benoitGIRAUD/NGL_PROTO_ST/Output/PNG/NGL_Proto_BOT.png

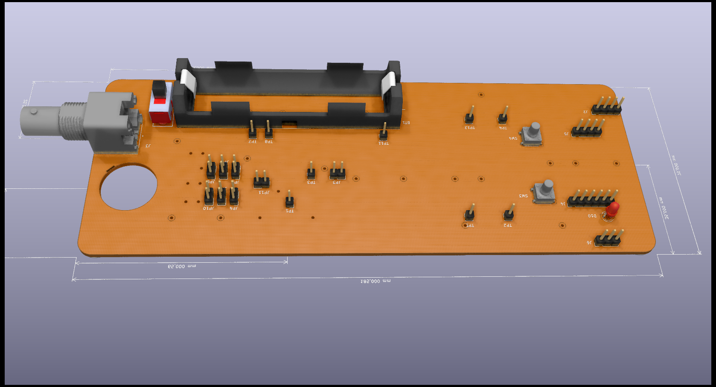
Output/PNG/NGL_Proto_BOT.png
