benoitGIRAUD/NGL_PROTO_ST/Output/PNG/NGL_Proto_TOP.png

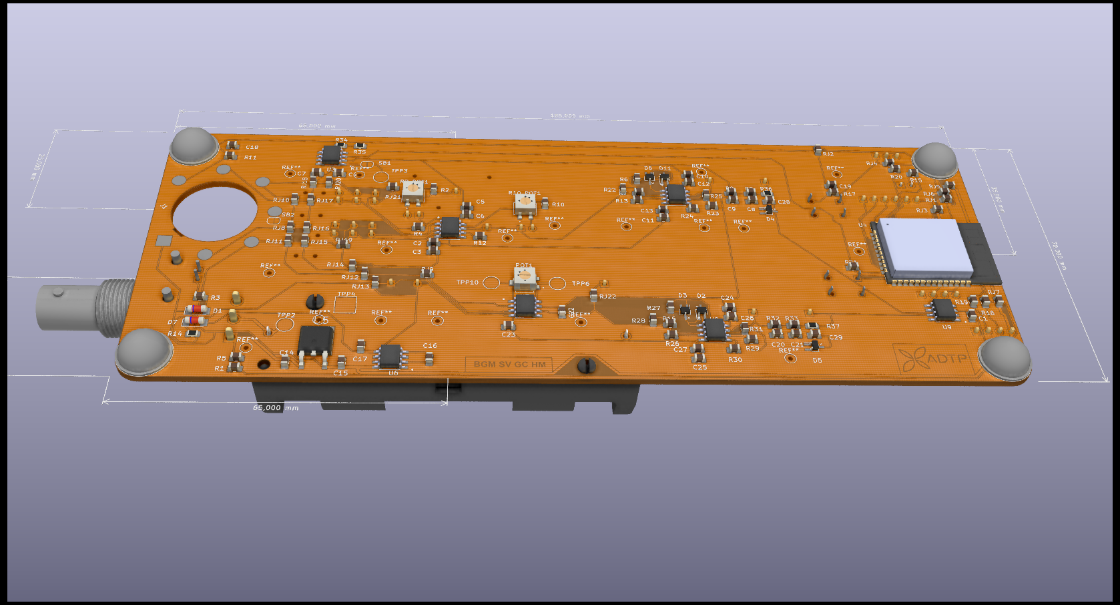
Output/PNG/NGL_Proto_TOP.png
