benoitGIRAUD/NGL_PROTO_ST/Lib_NGL_Proto/3224X-1-103E.STEP

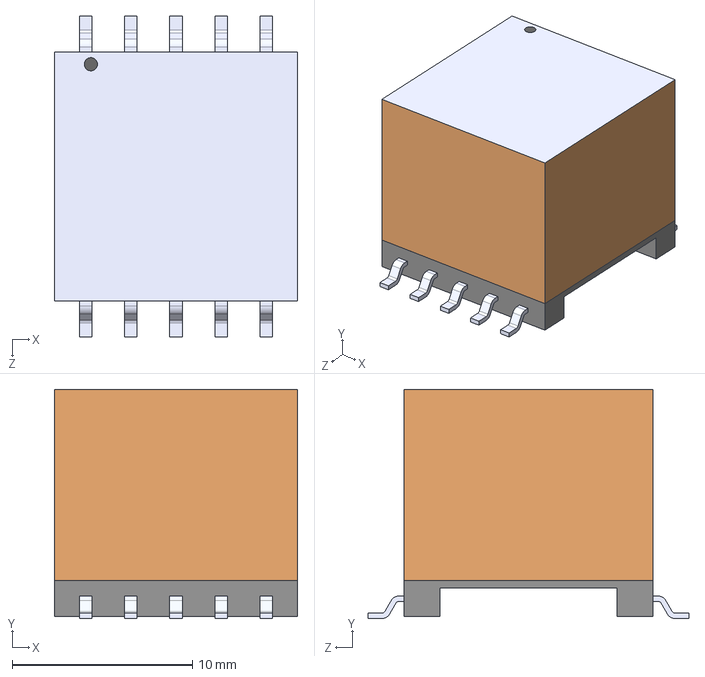
[picture p25: CAD file, 2022-05-25]
Lib_NGL_Proto/3224X-1-103E.STEP
13.5 x 12.7 x 17.8 mm
