benoitGIRAUD/NGL_PROTO_ST/Lib_NGL_Proto/5227161-2.step

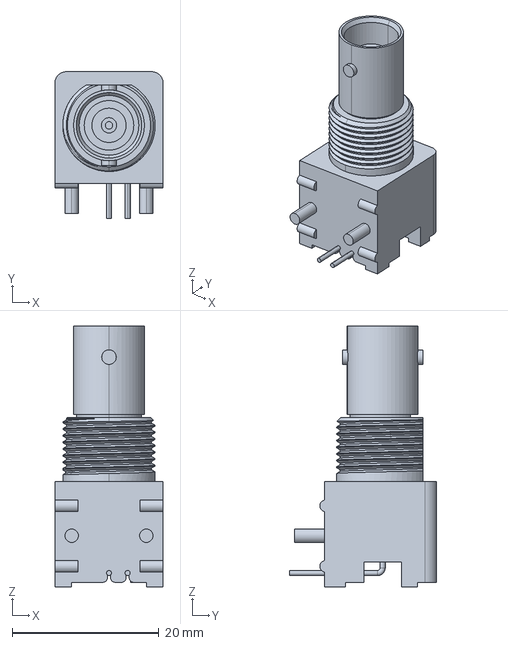
[picture p26: CAD file, 2022-05-25]
Lib_NGL_Proto/5227161-2.step
14.8 x 20.0 x 35.6 mm
