benoitGIRAUD/NGL_PROTO_ST/Output/SCH/NGL_Proto_PROD.pdf

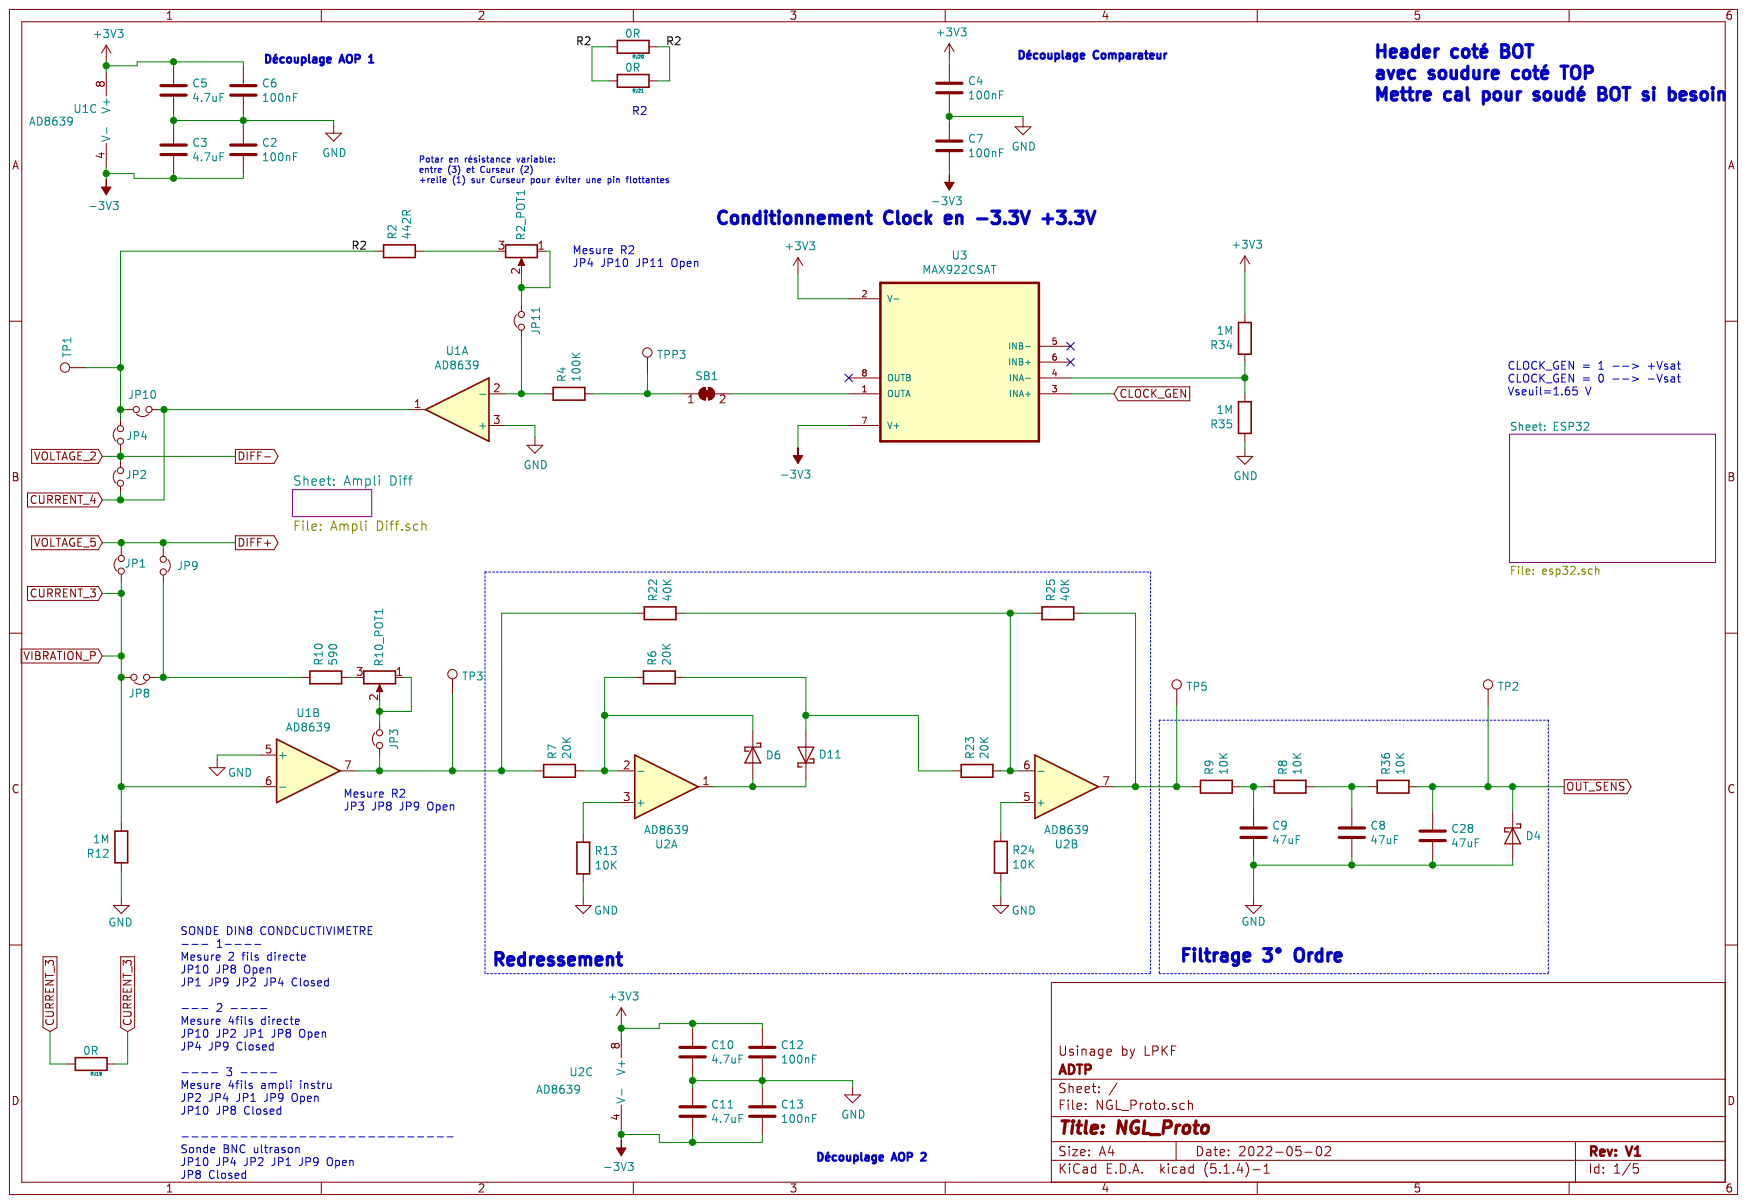
[picture p29: page 1]

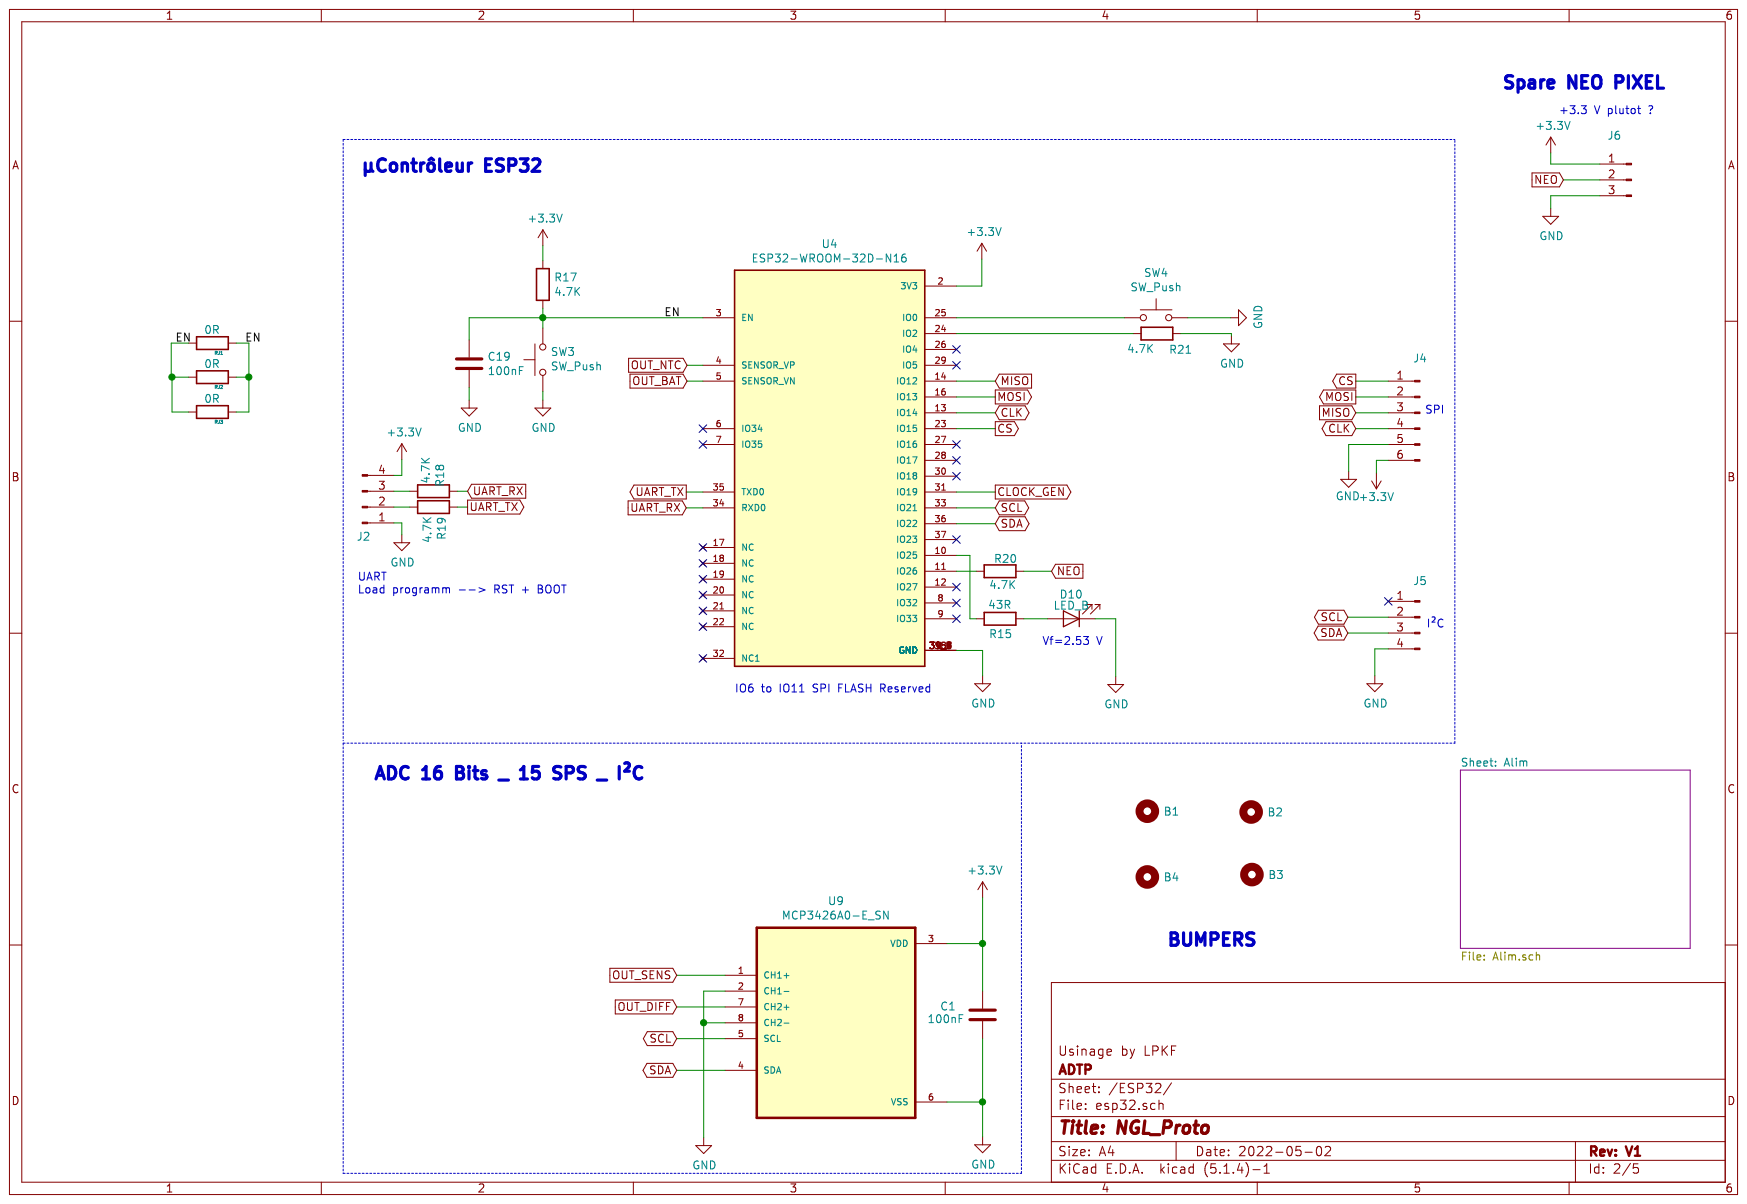
[picture p30: page 2]

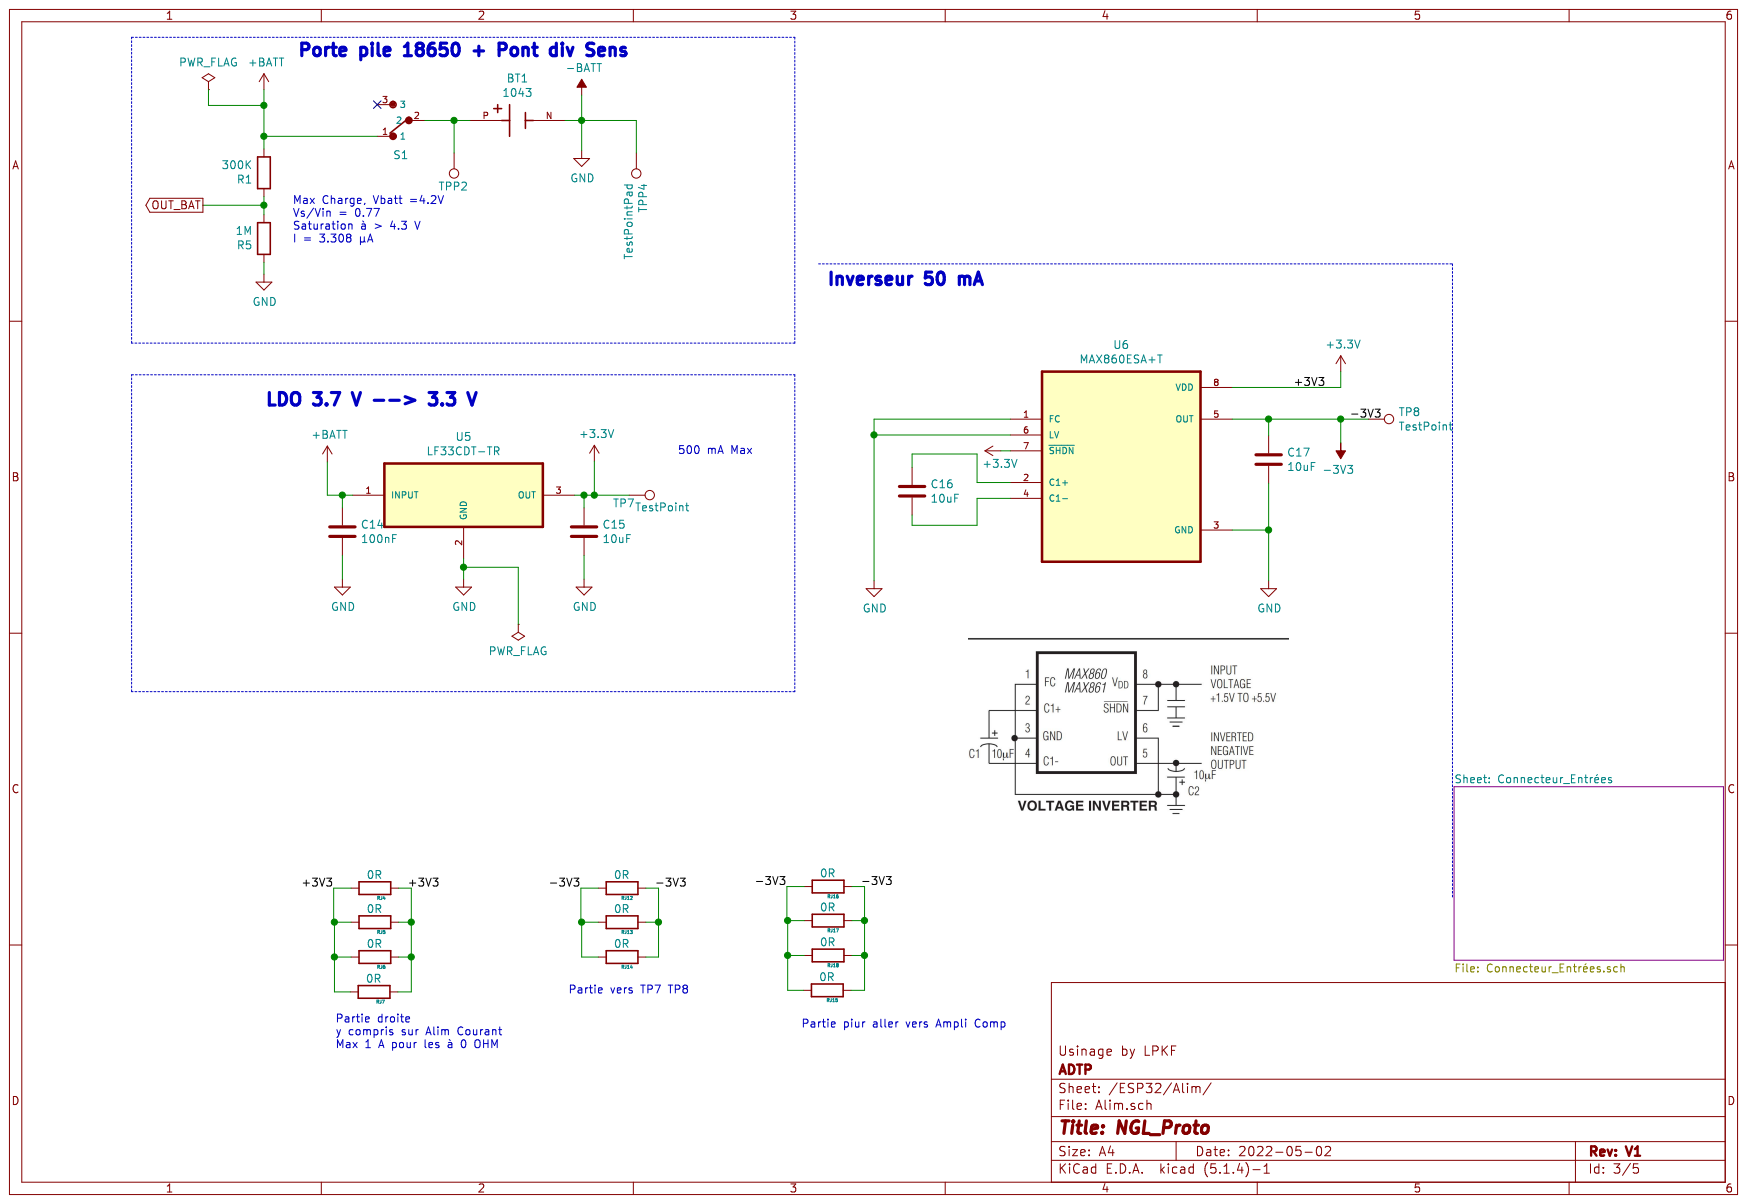
[picture p31: page 3]

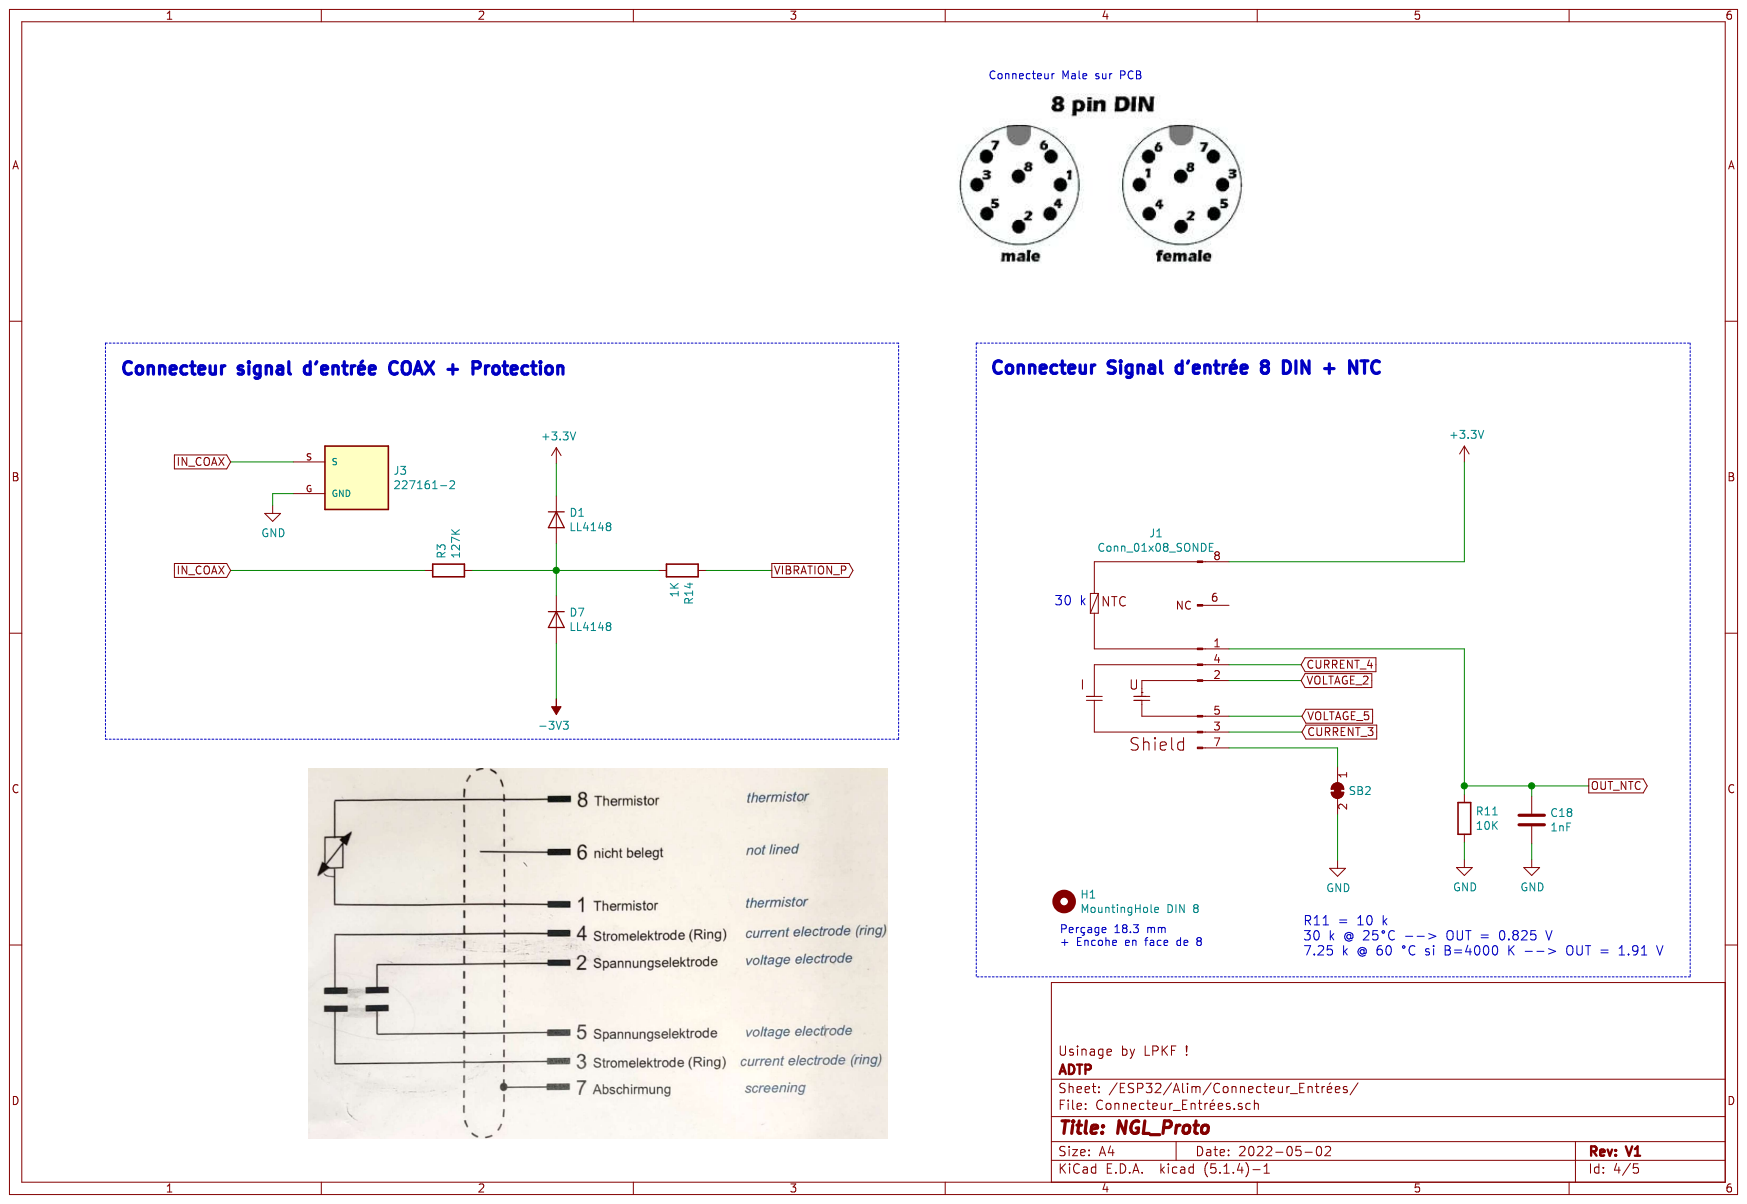
[picture p32: page 4]

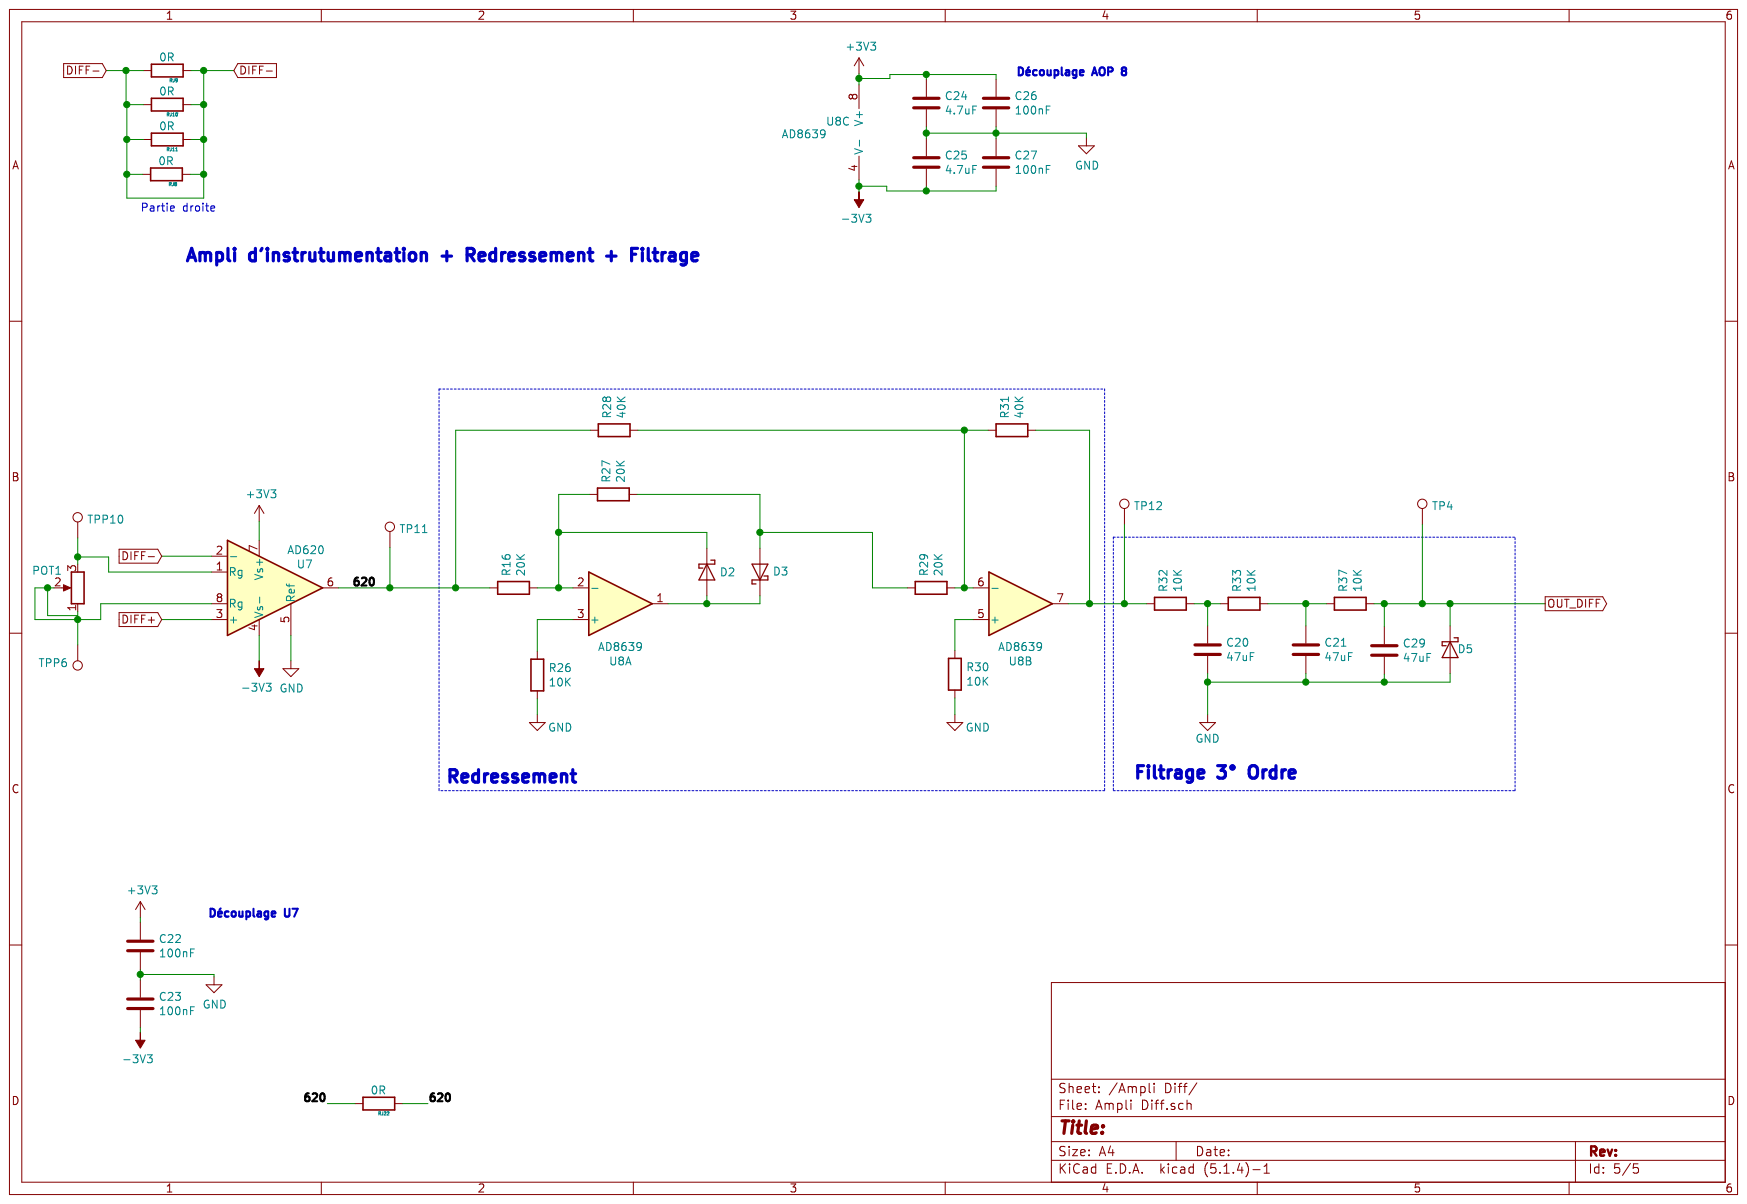
[picture p33: page 5]
