benoitGIRAUD/NGL_PROTO_ST/Output/SCH/NGL_Proto_V1.pdf

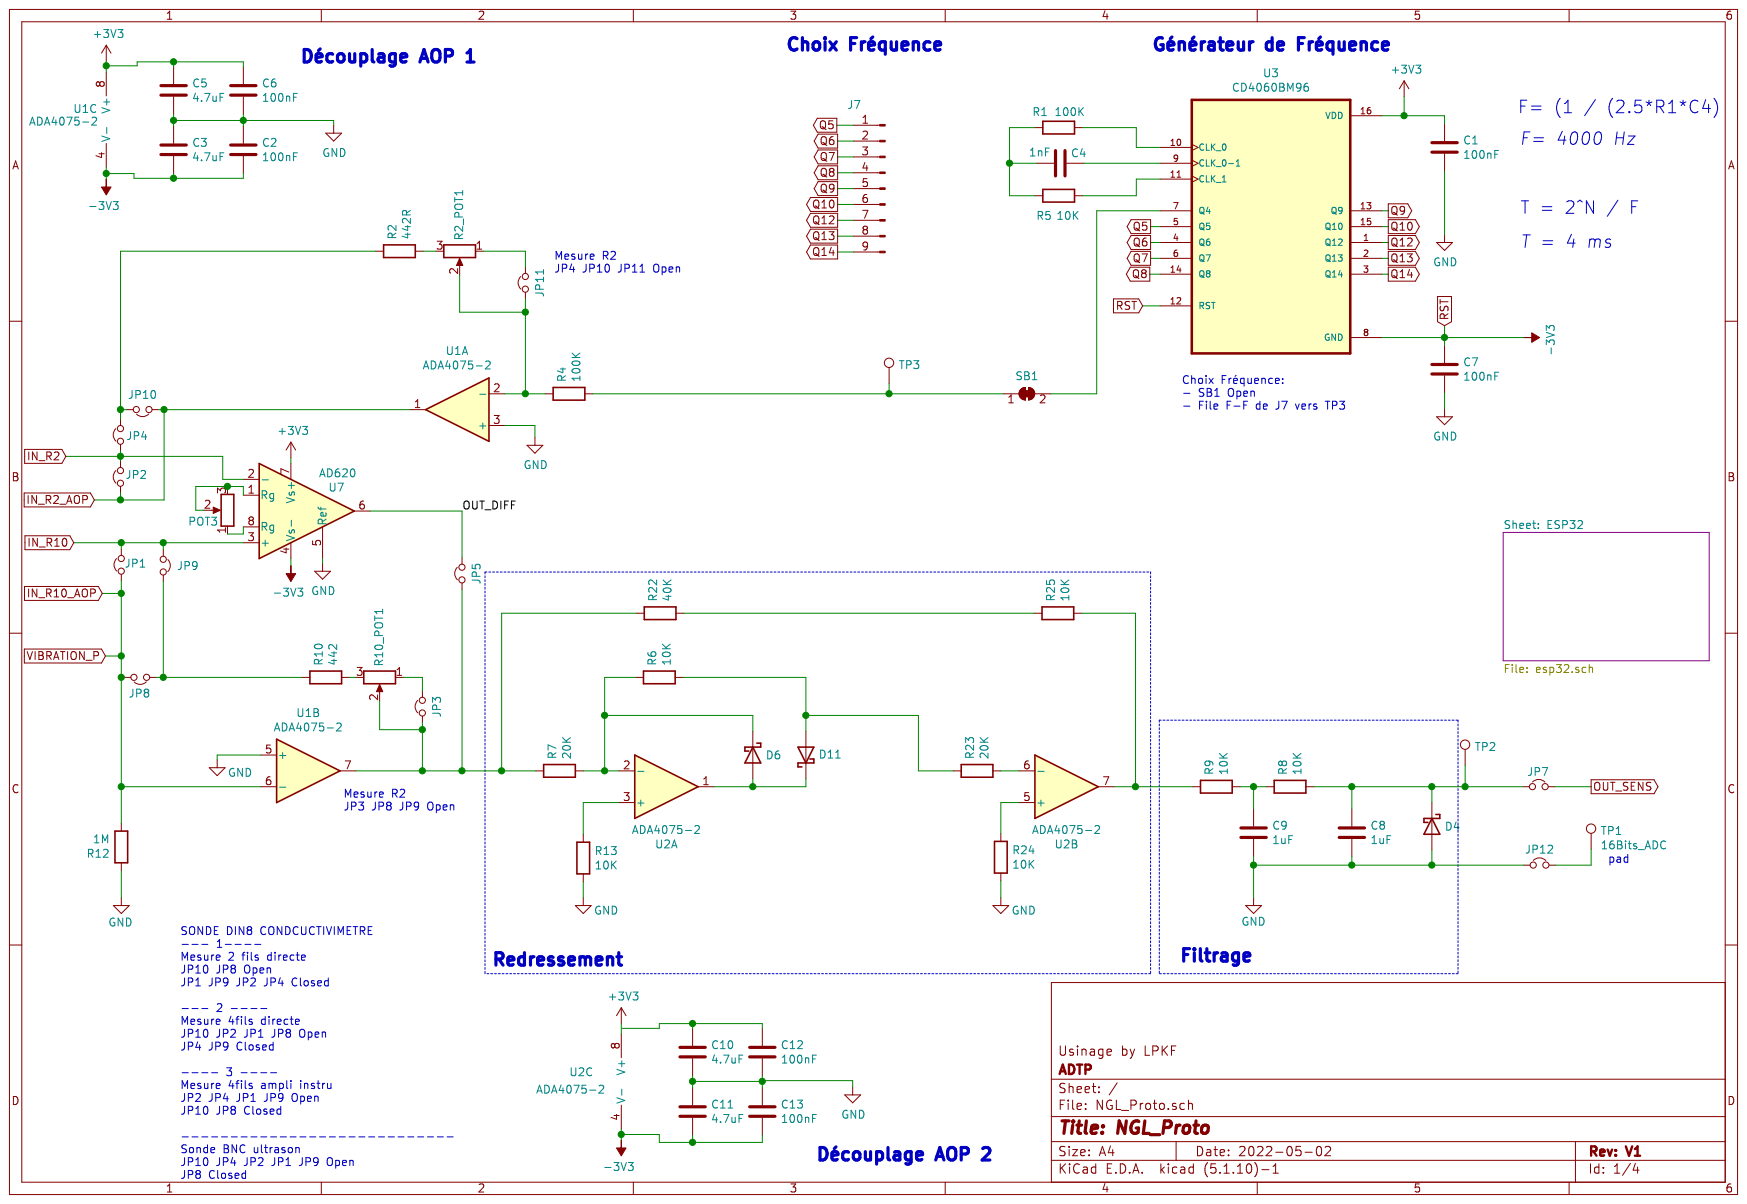
[picture p34: page 1]

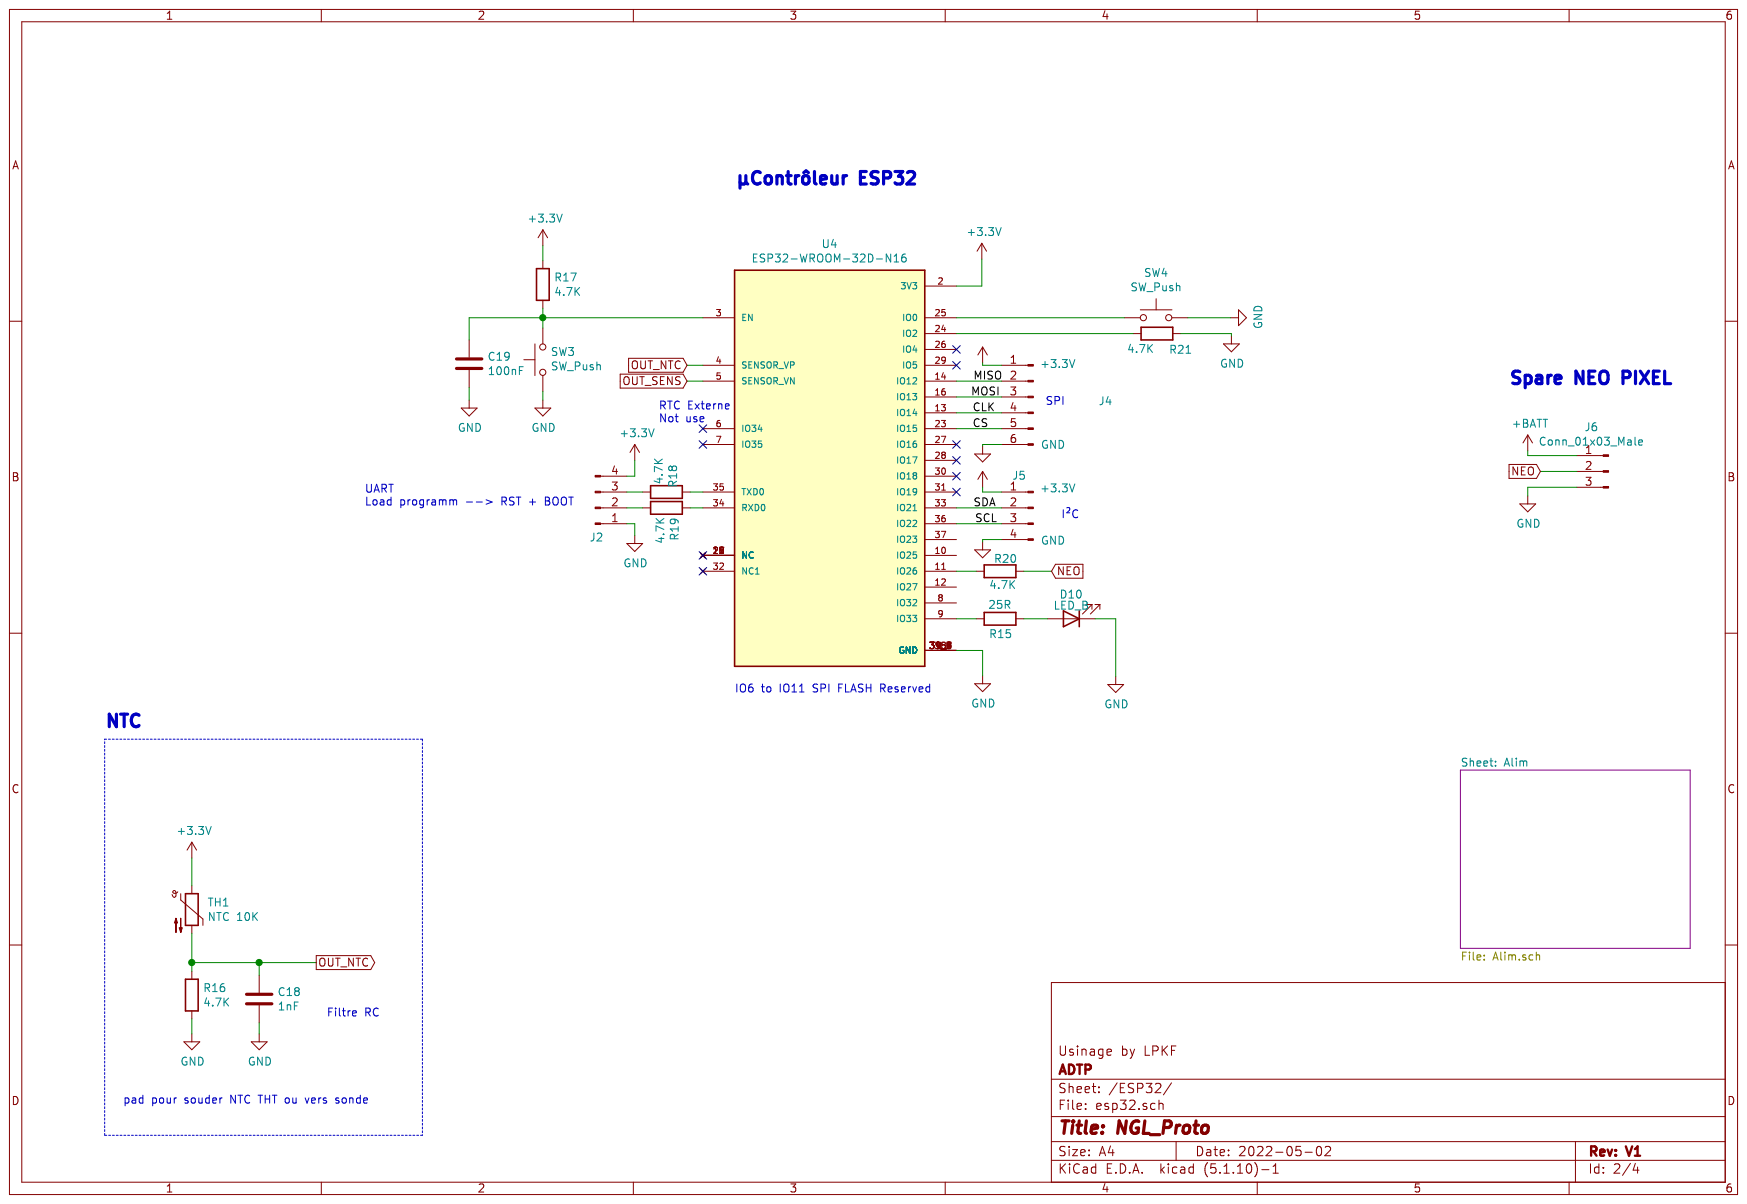
[picture p35: page 2]

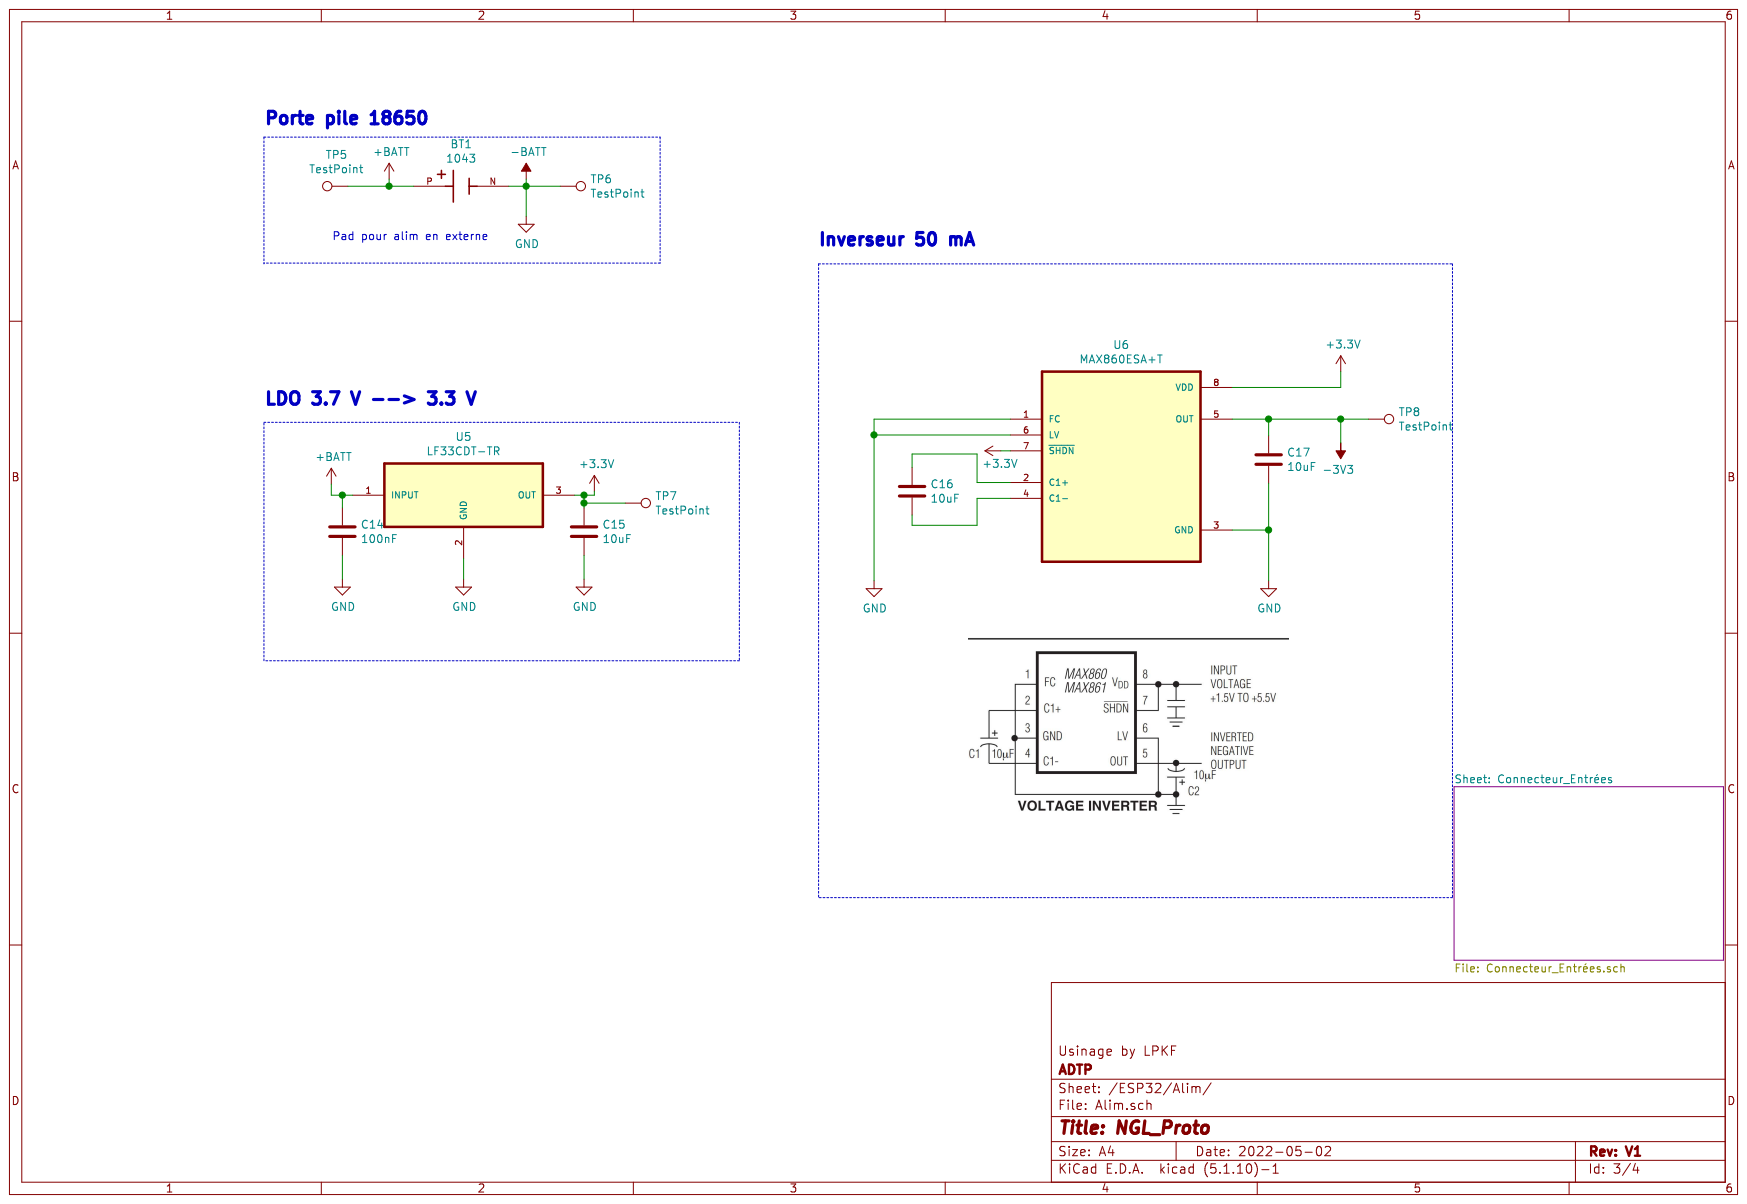
[picture p36: page 3]

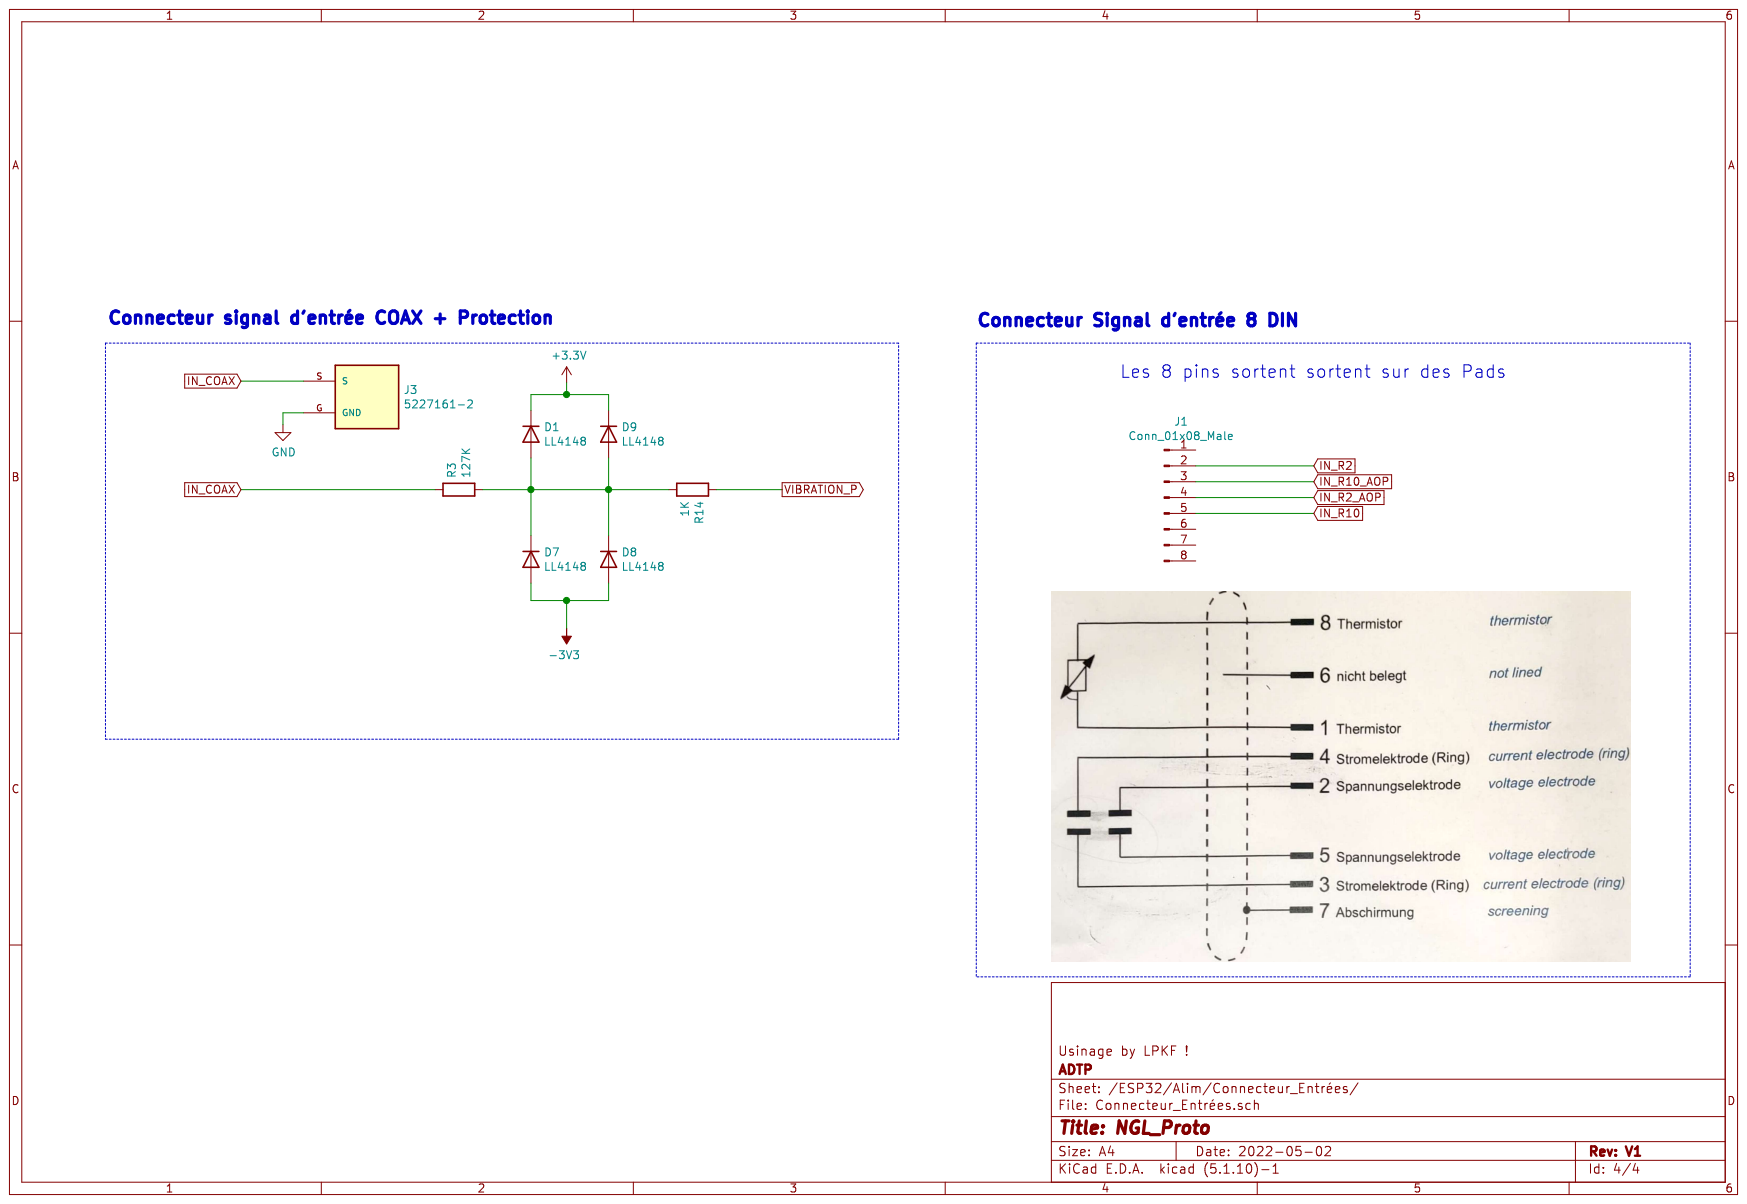
[picture p37: page 4]
