benoitGIRAUD/NGL_PROTO_ST/Output/SCH/NGL_Proto_V1_11-05.pdf

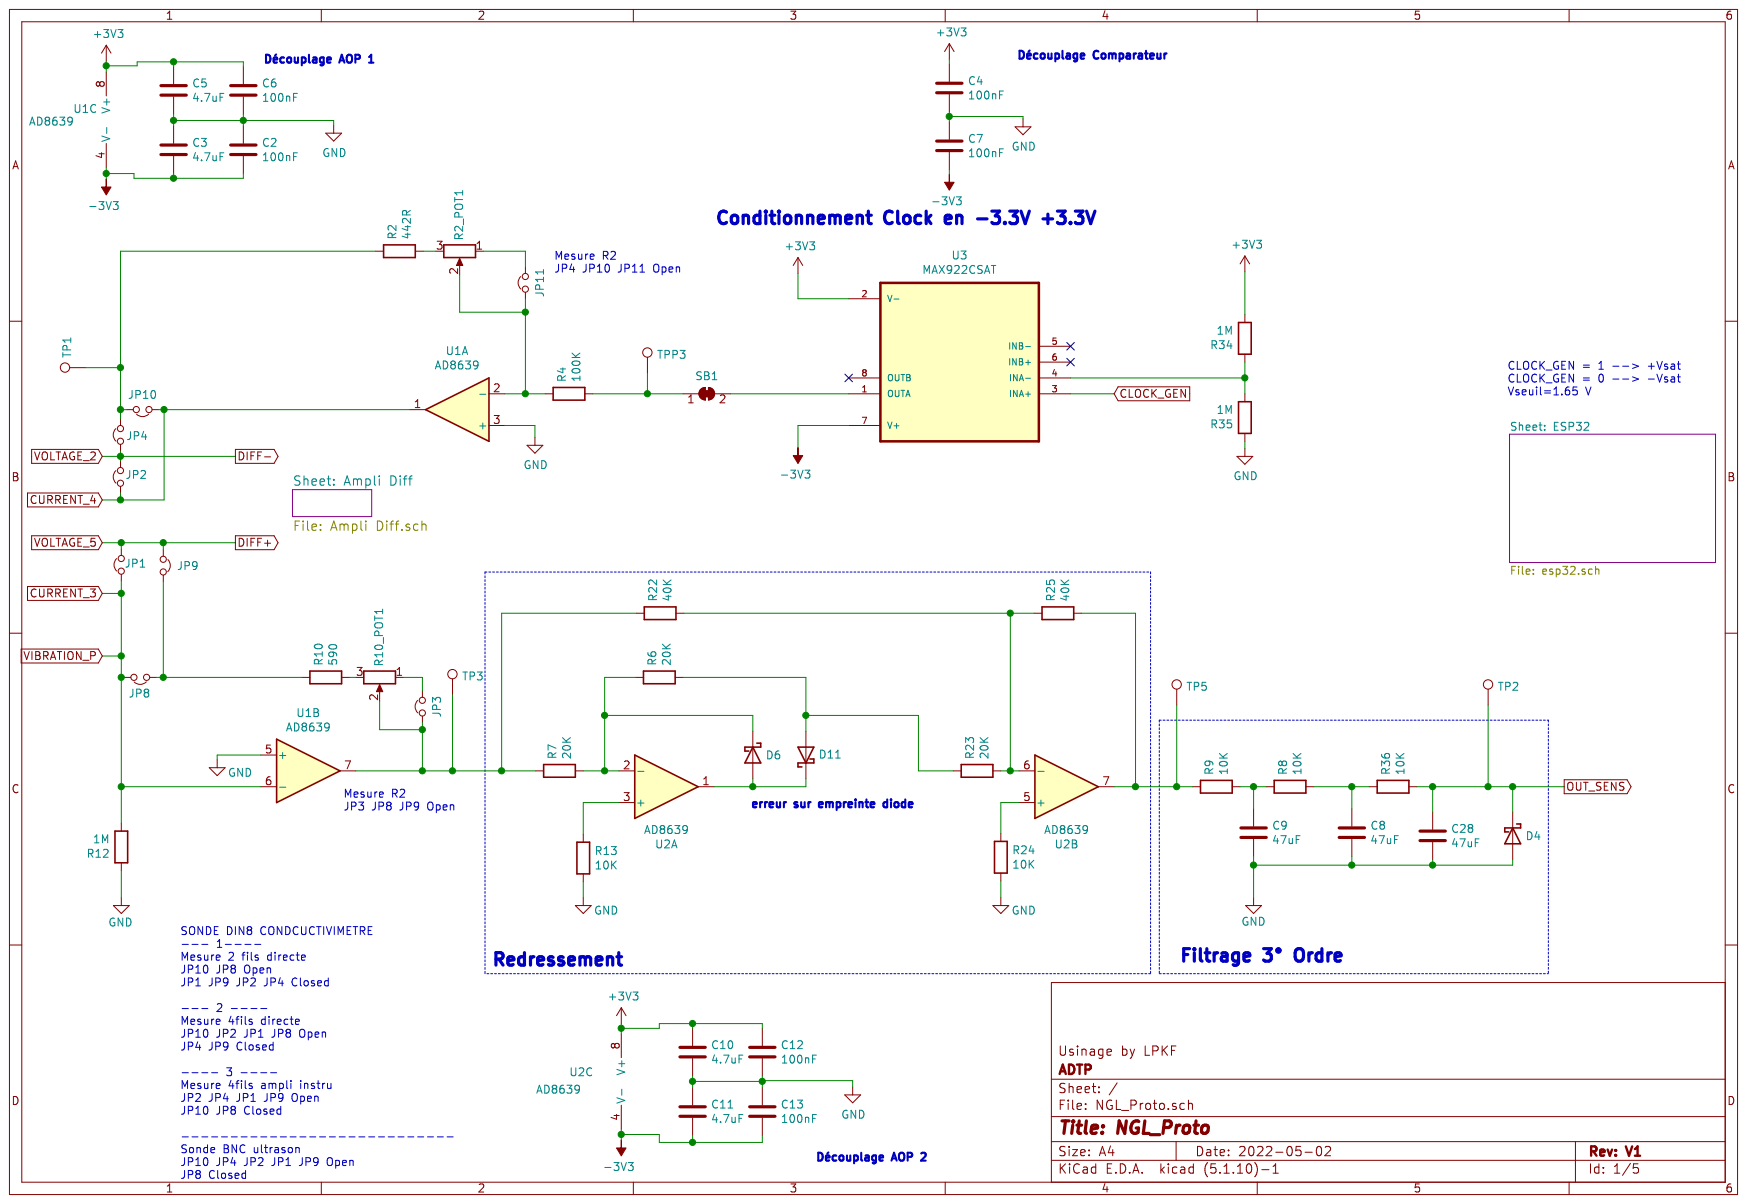
[picture p38: page 1]

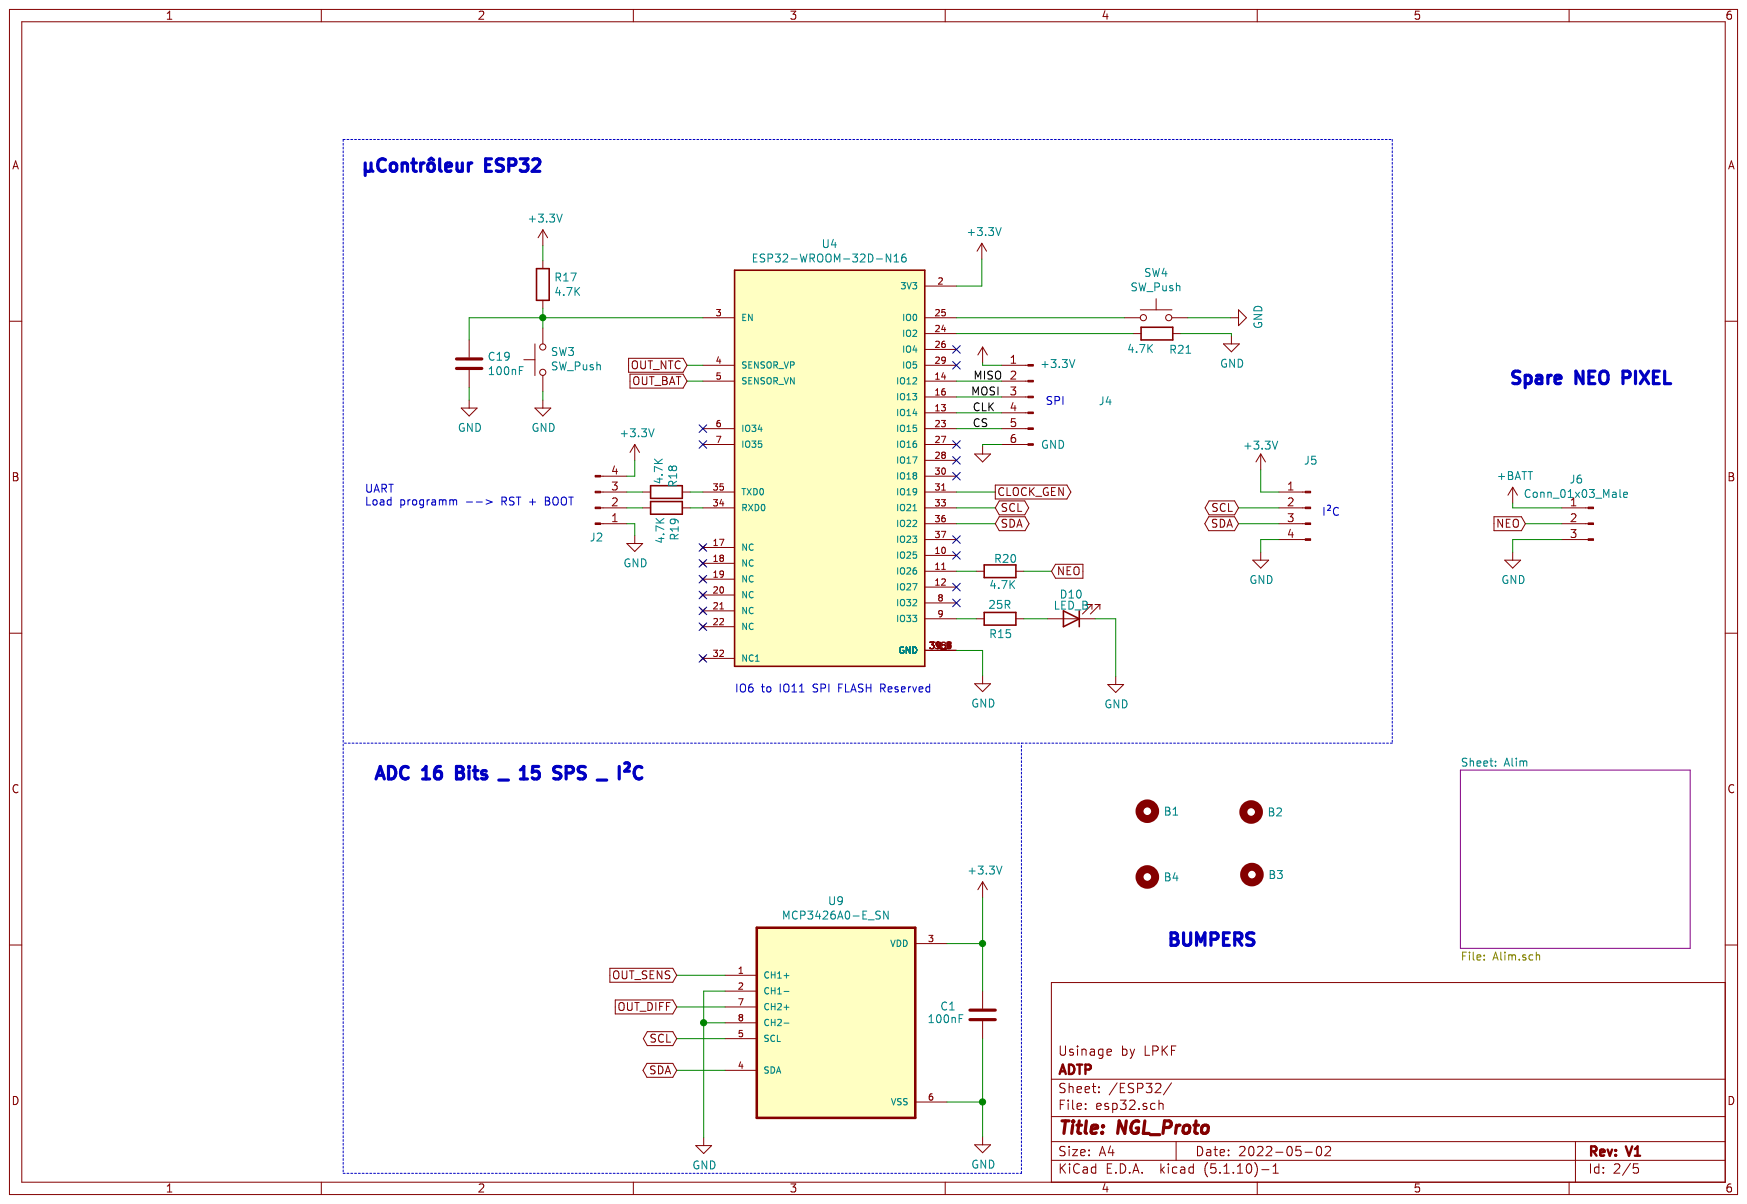
[picture p39: page 2]

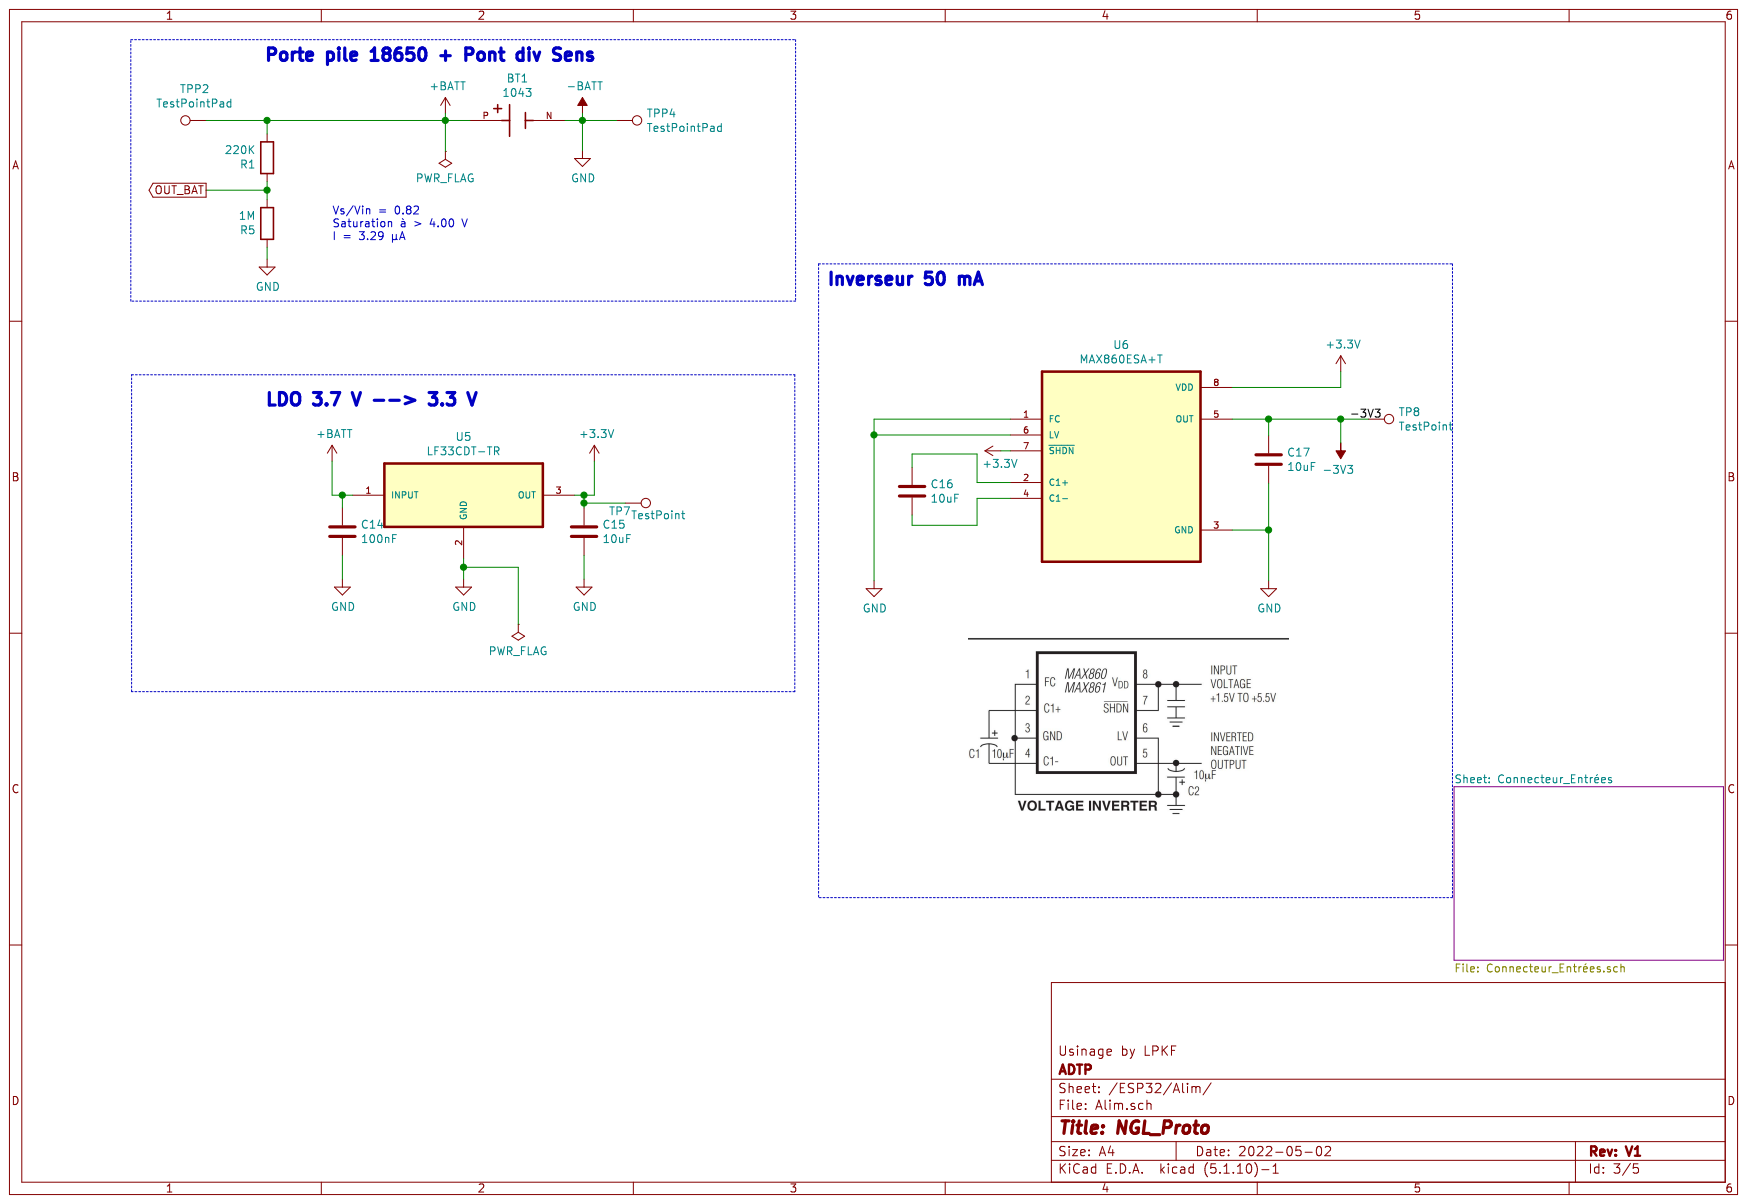
[picture p40: page 3]

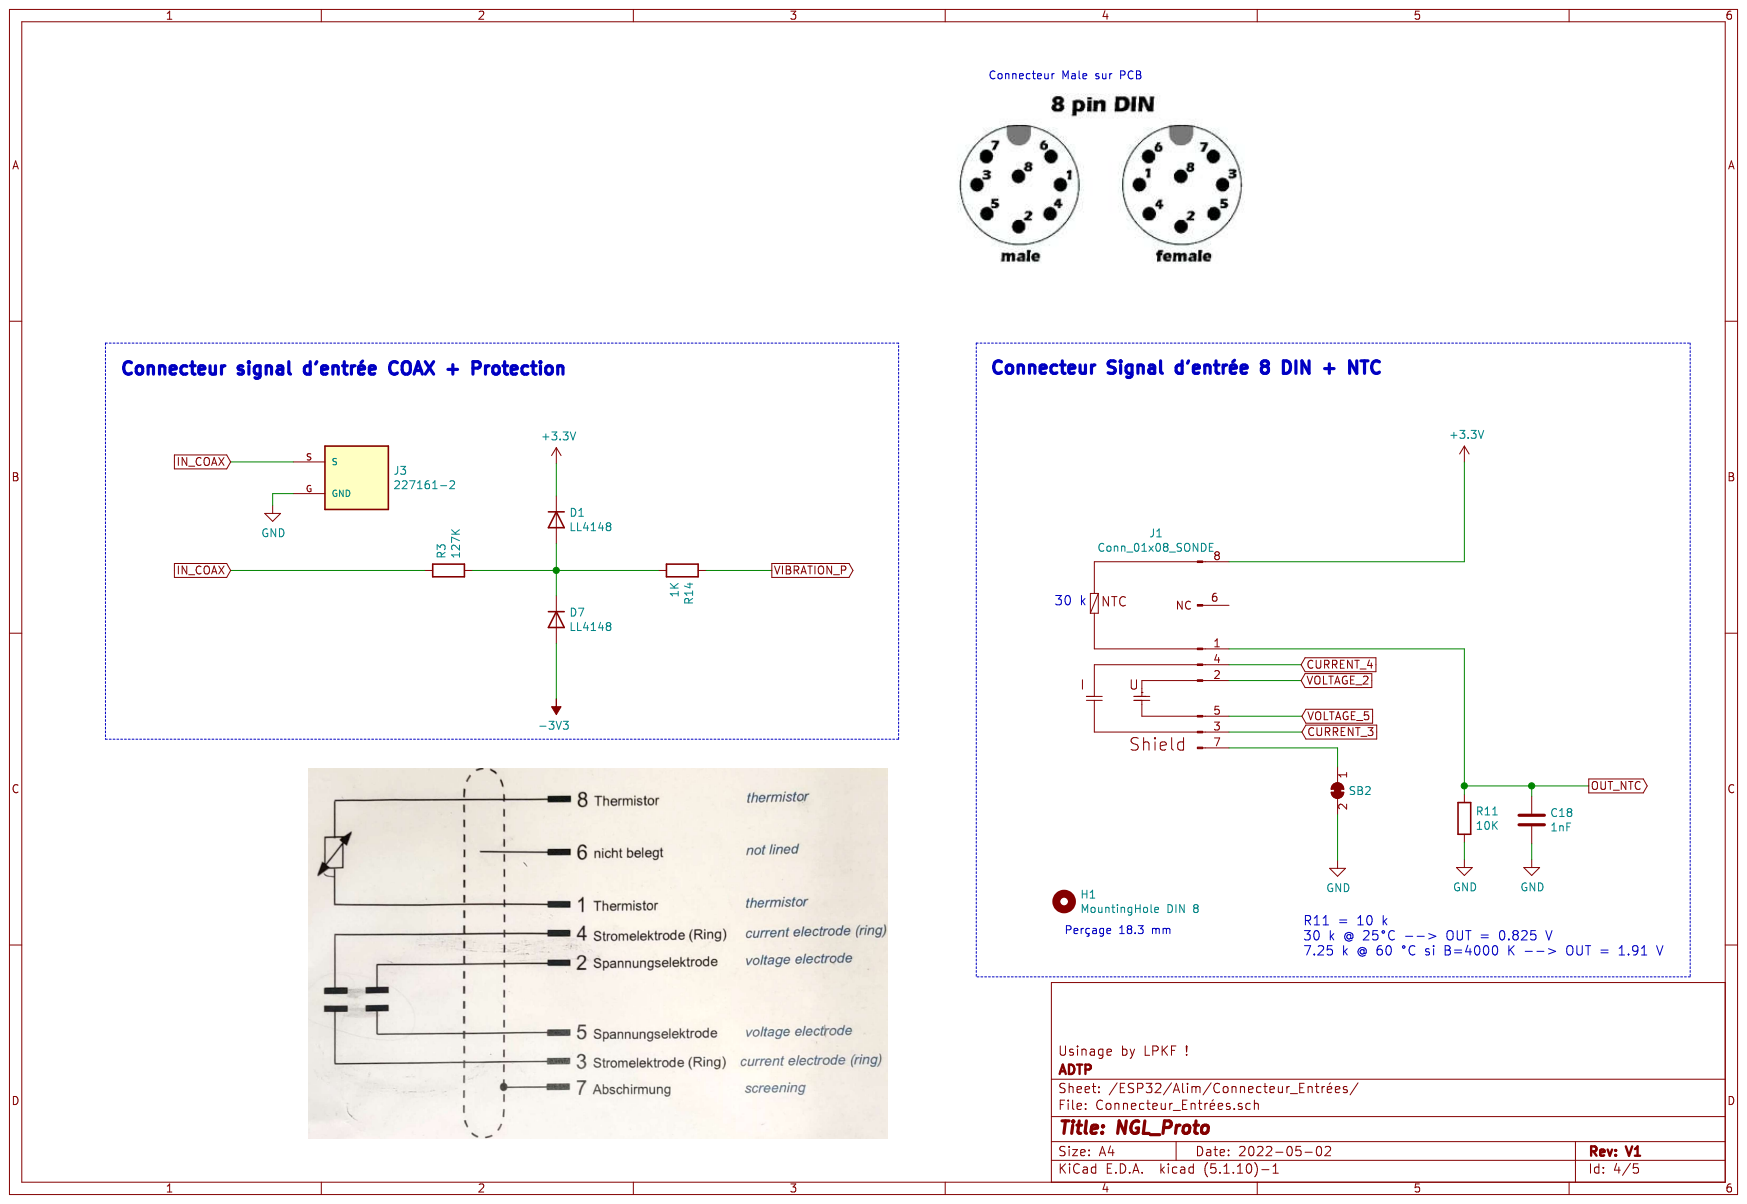
[picture p41: page 4]

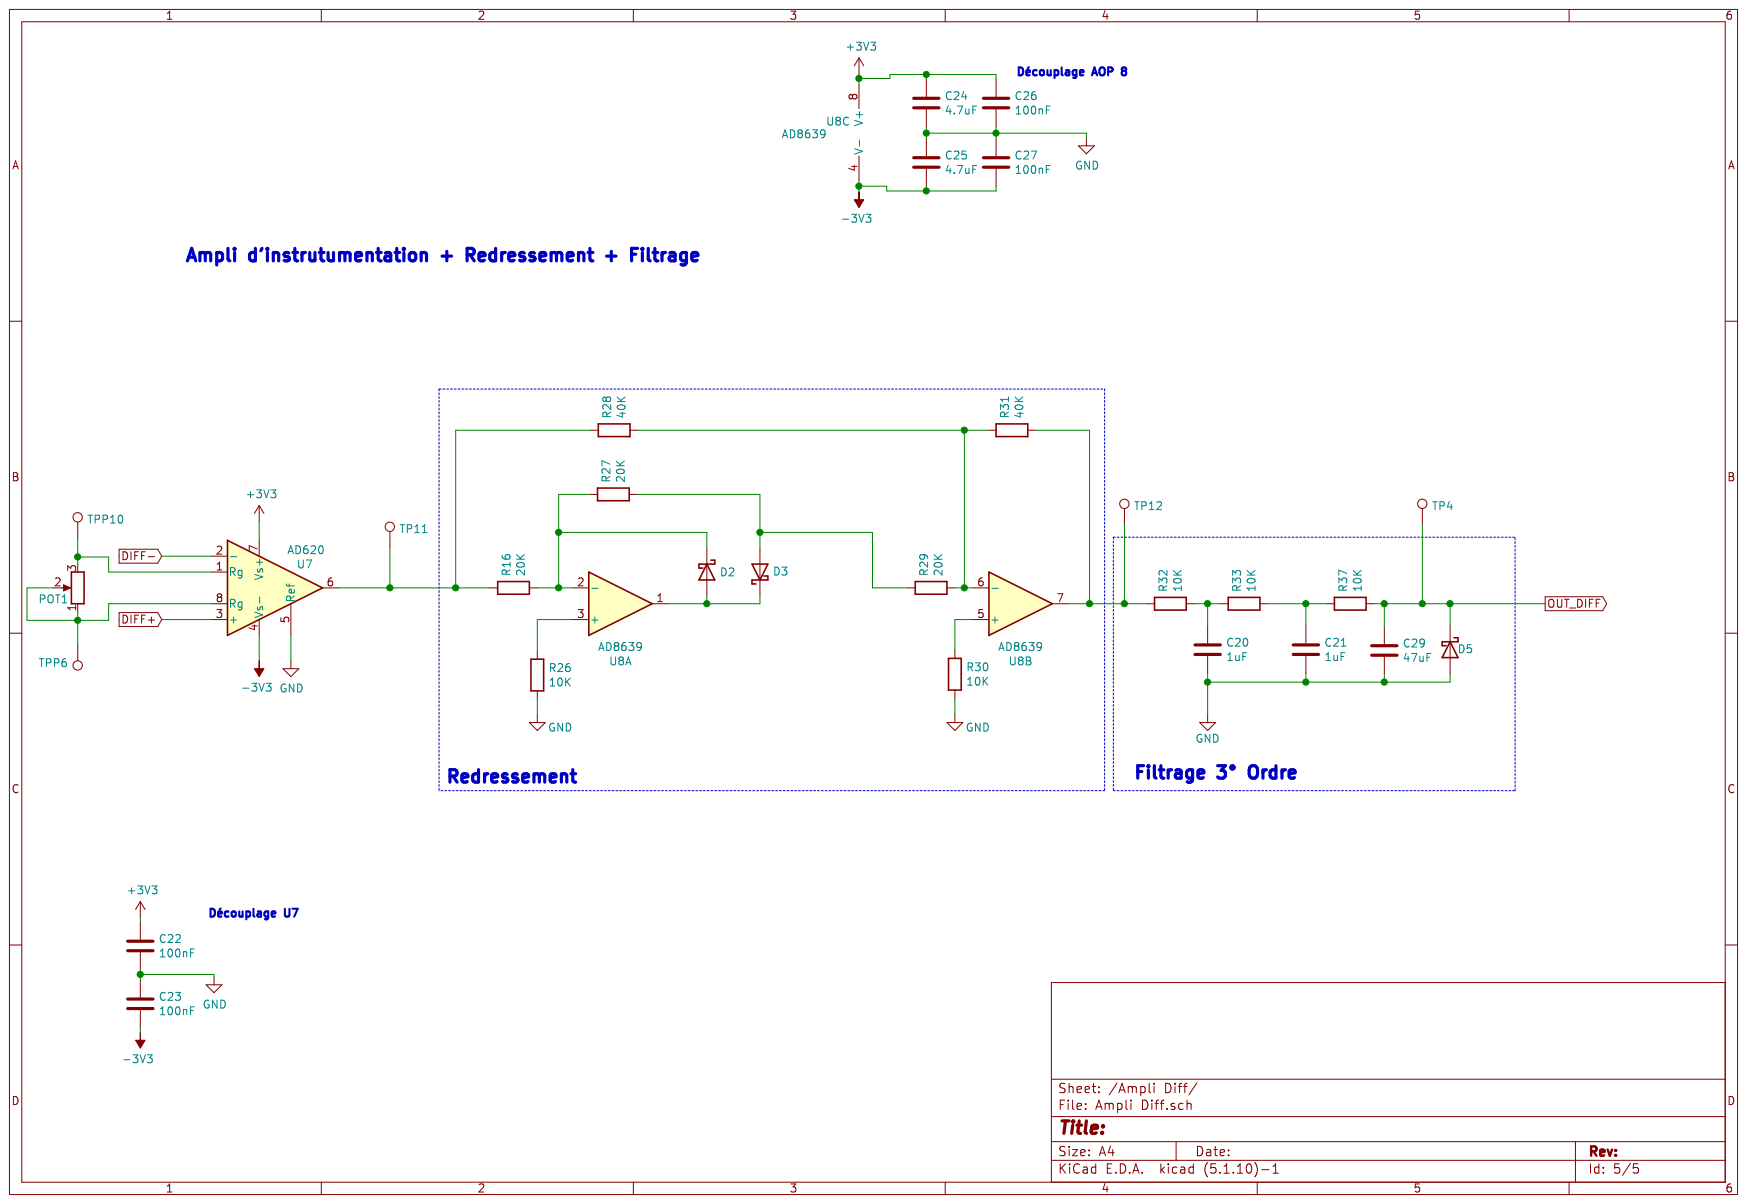
[picture p42: page 5]
