benoitGIRAUD/NGL_PROTO_ST/Output/SCH/NGL_Proto_V1_11-05_v2.pdf

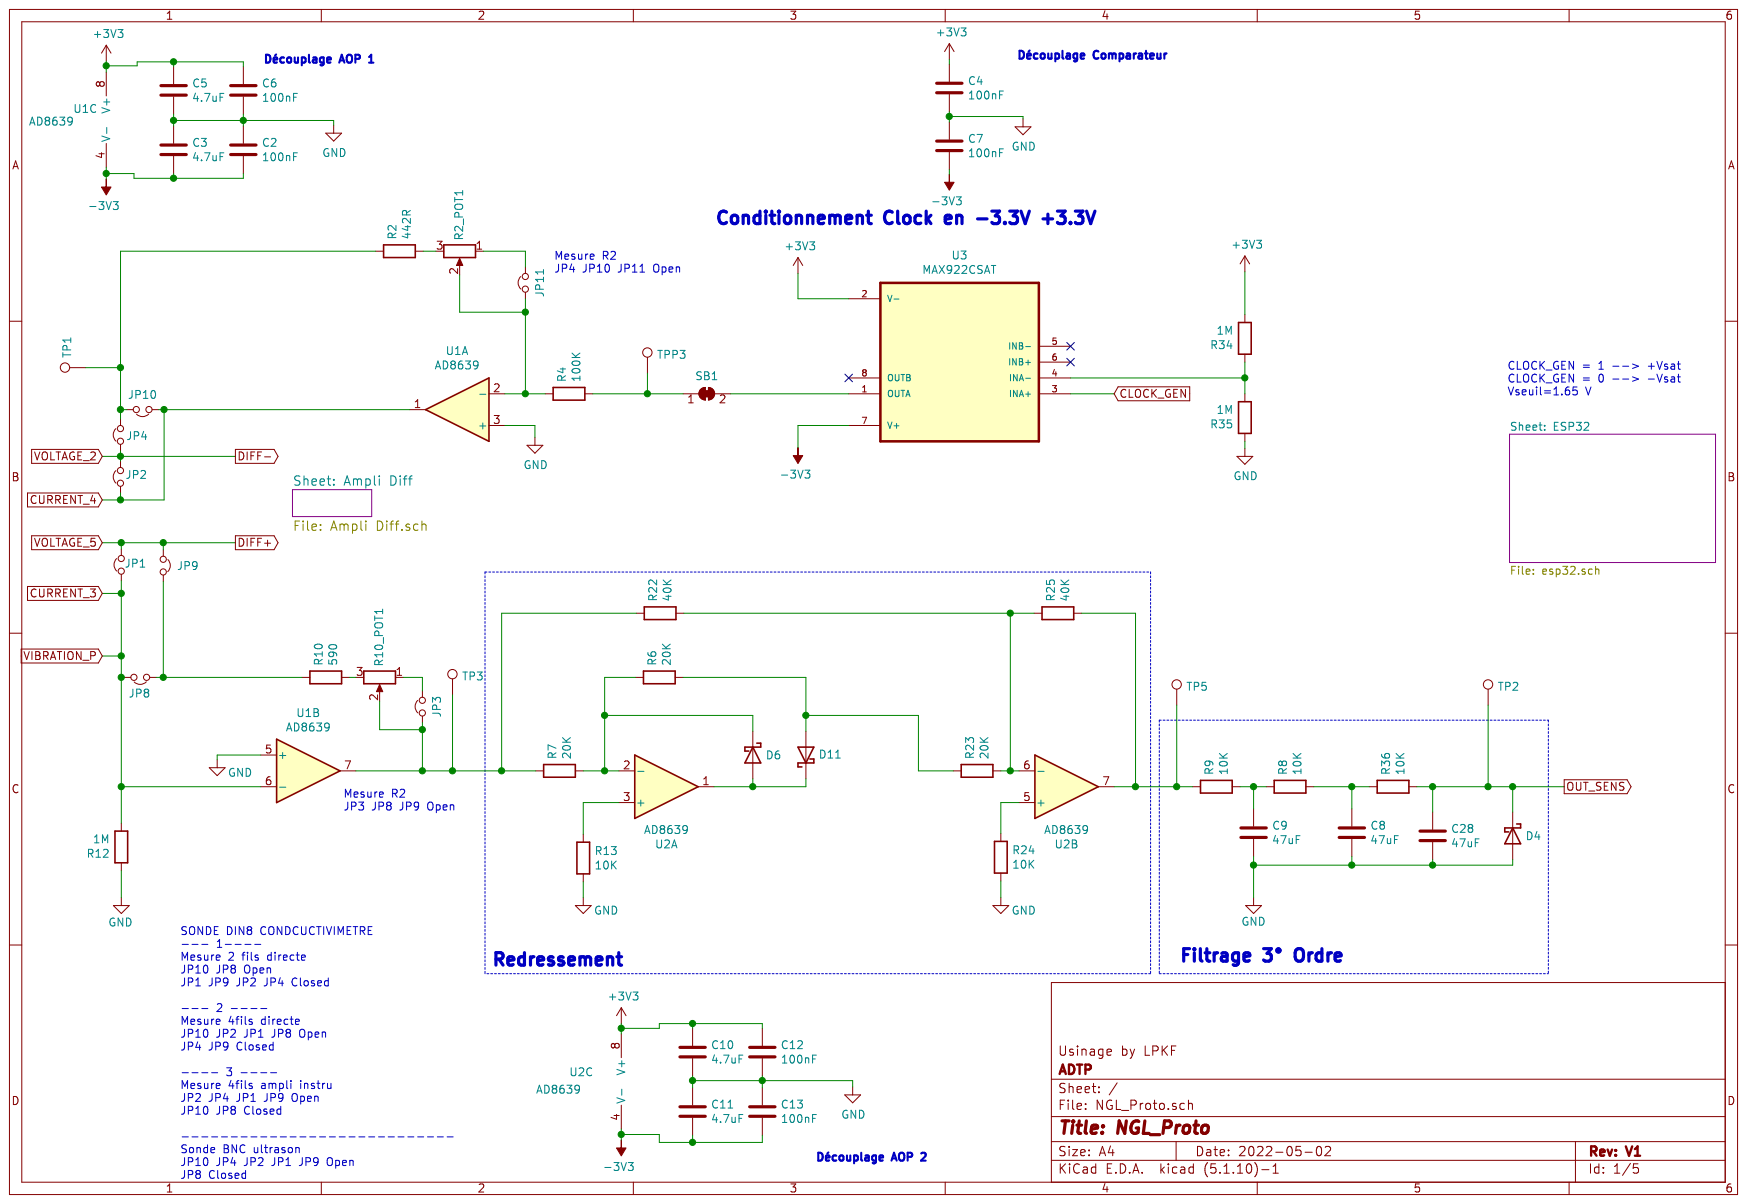
[picture p43: page 1]

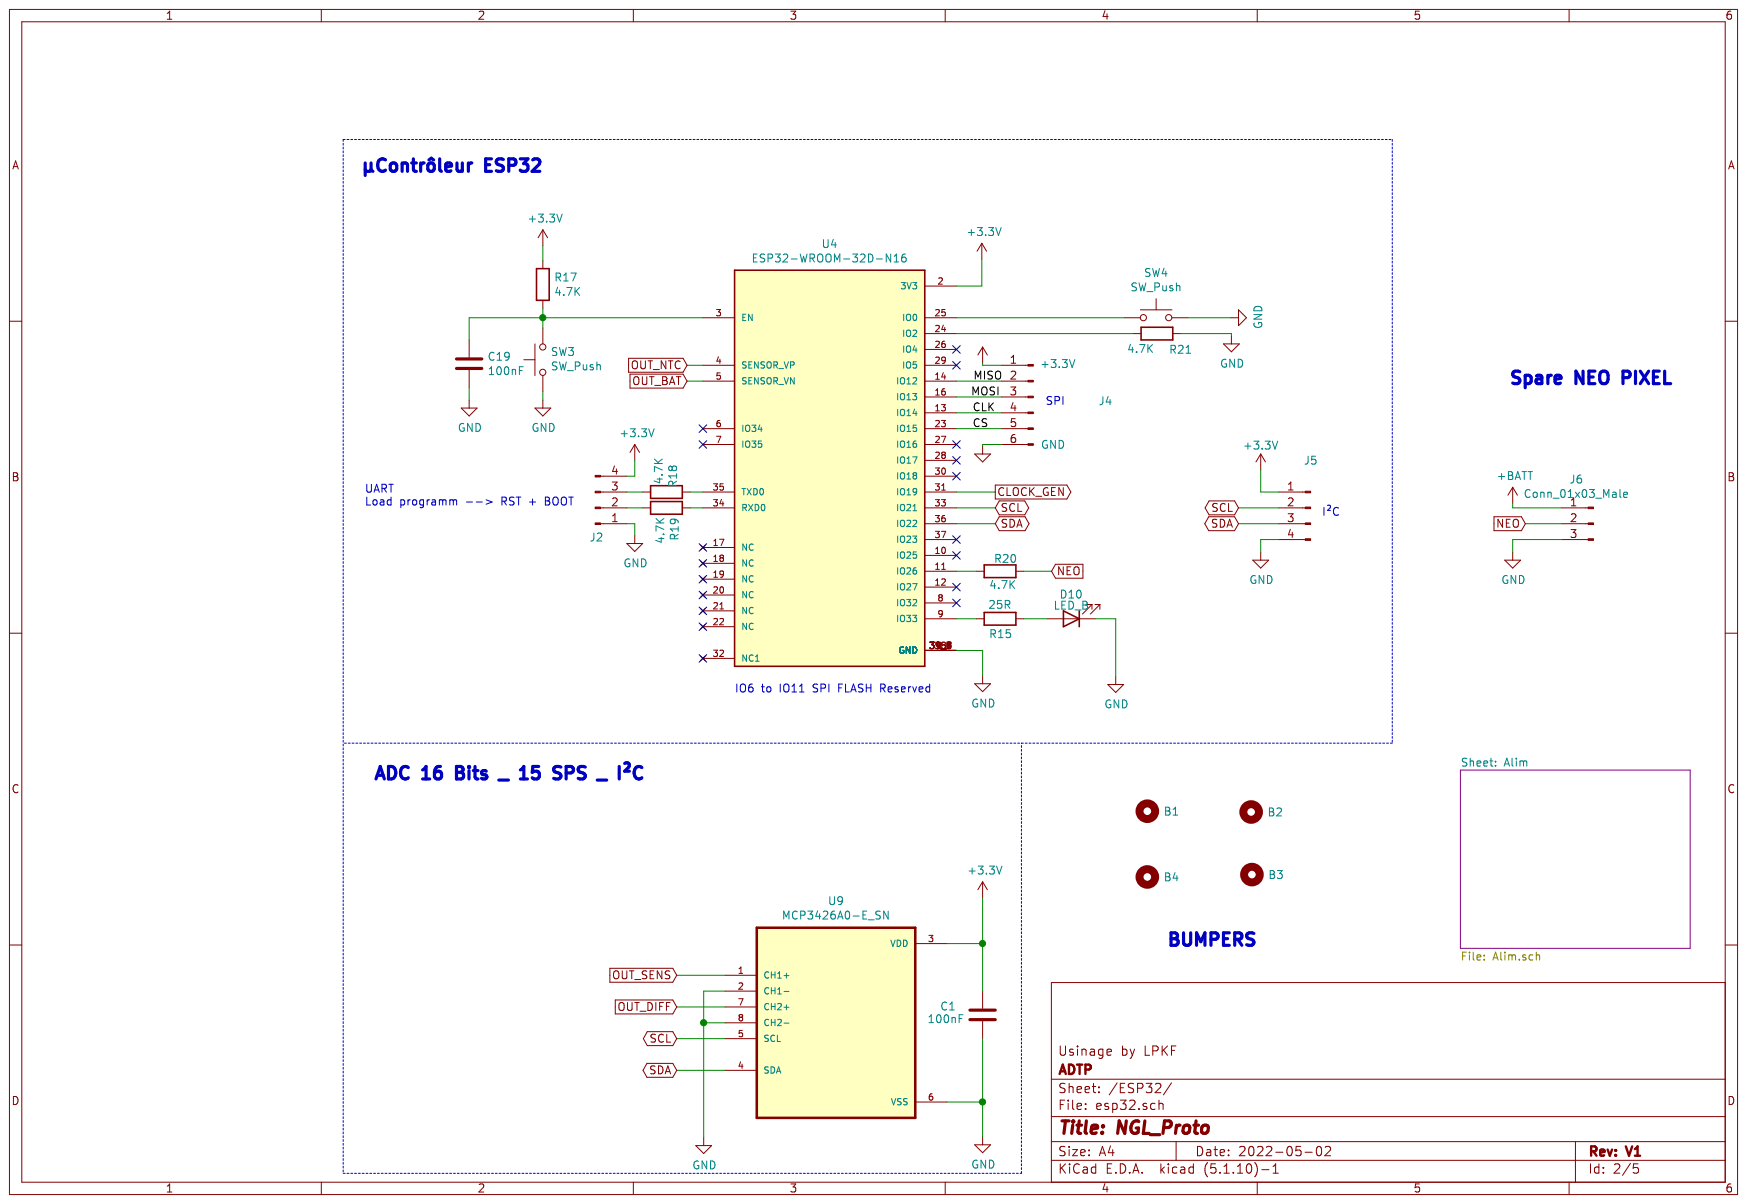
[picture p44: page 2]

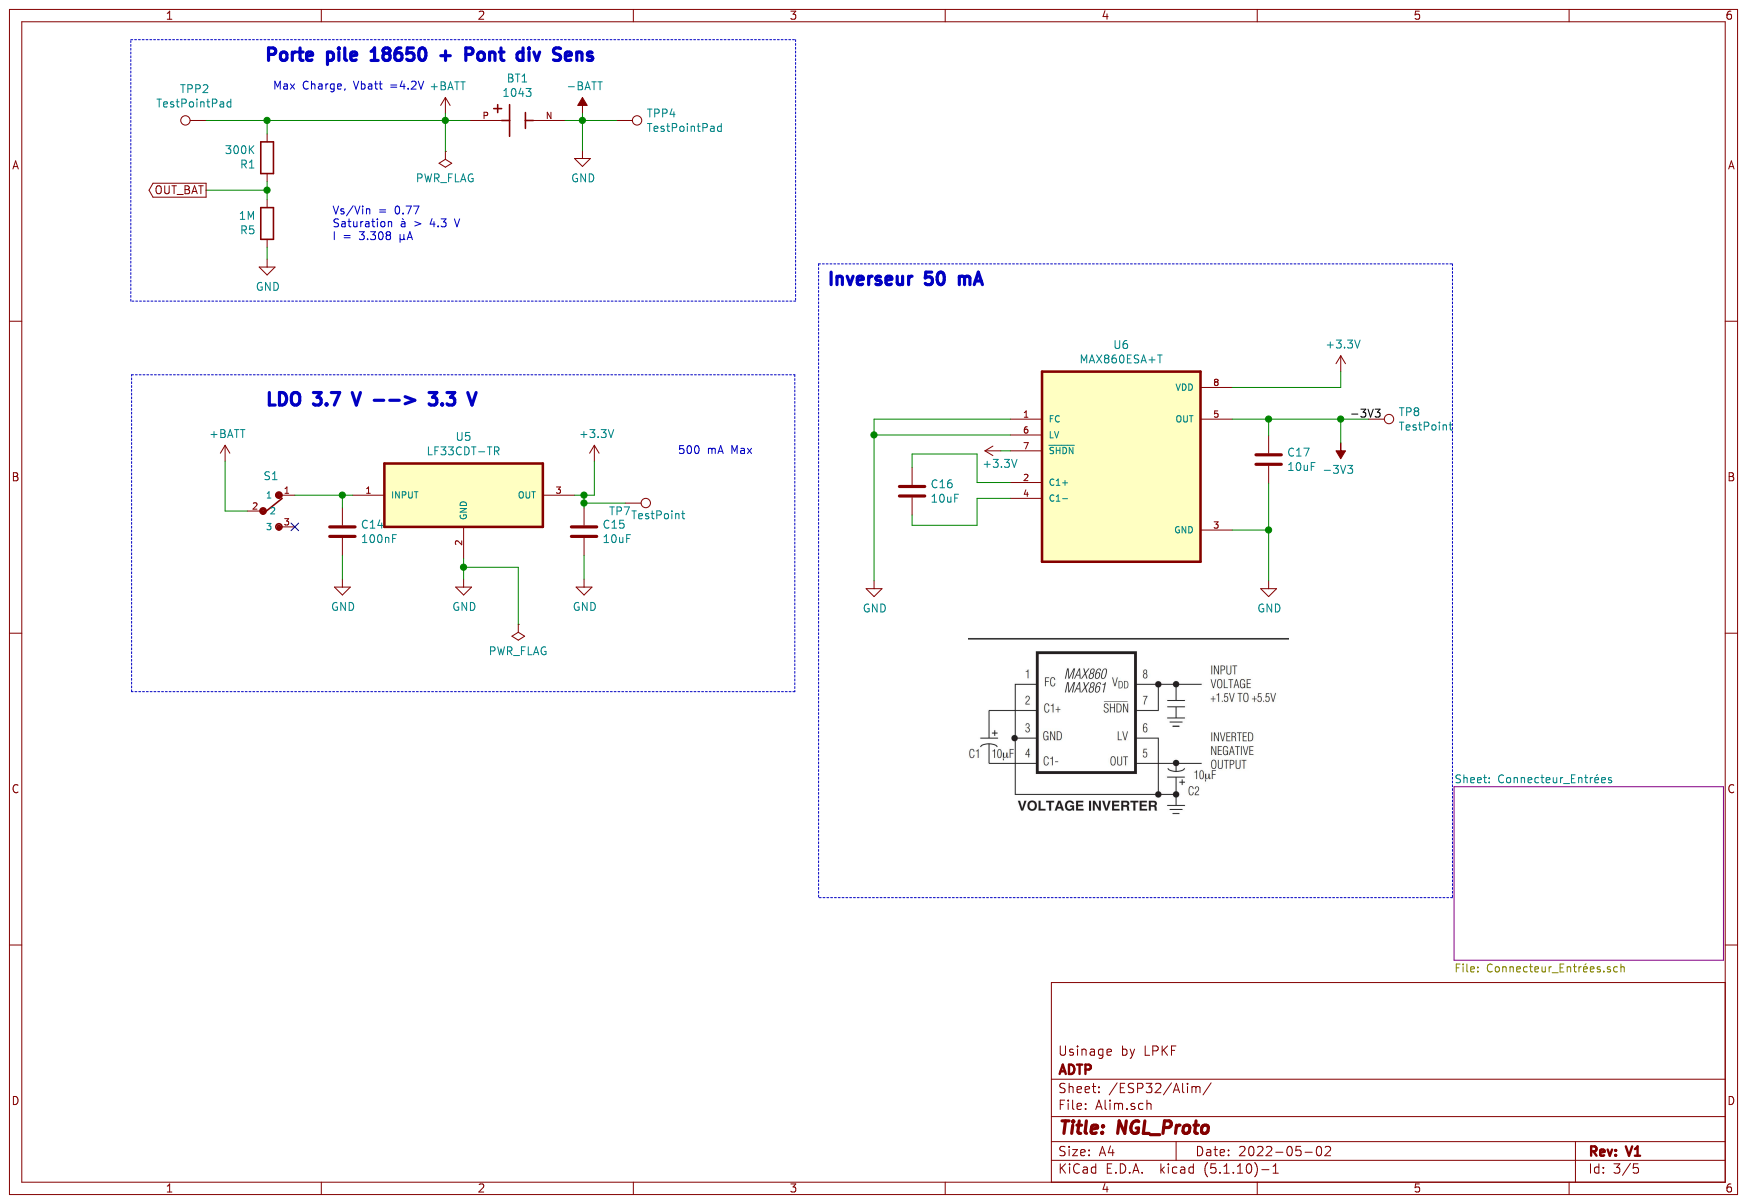
[picture p45: page 3]

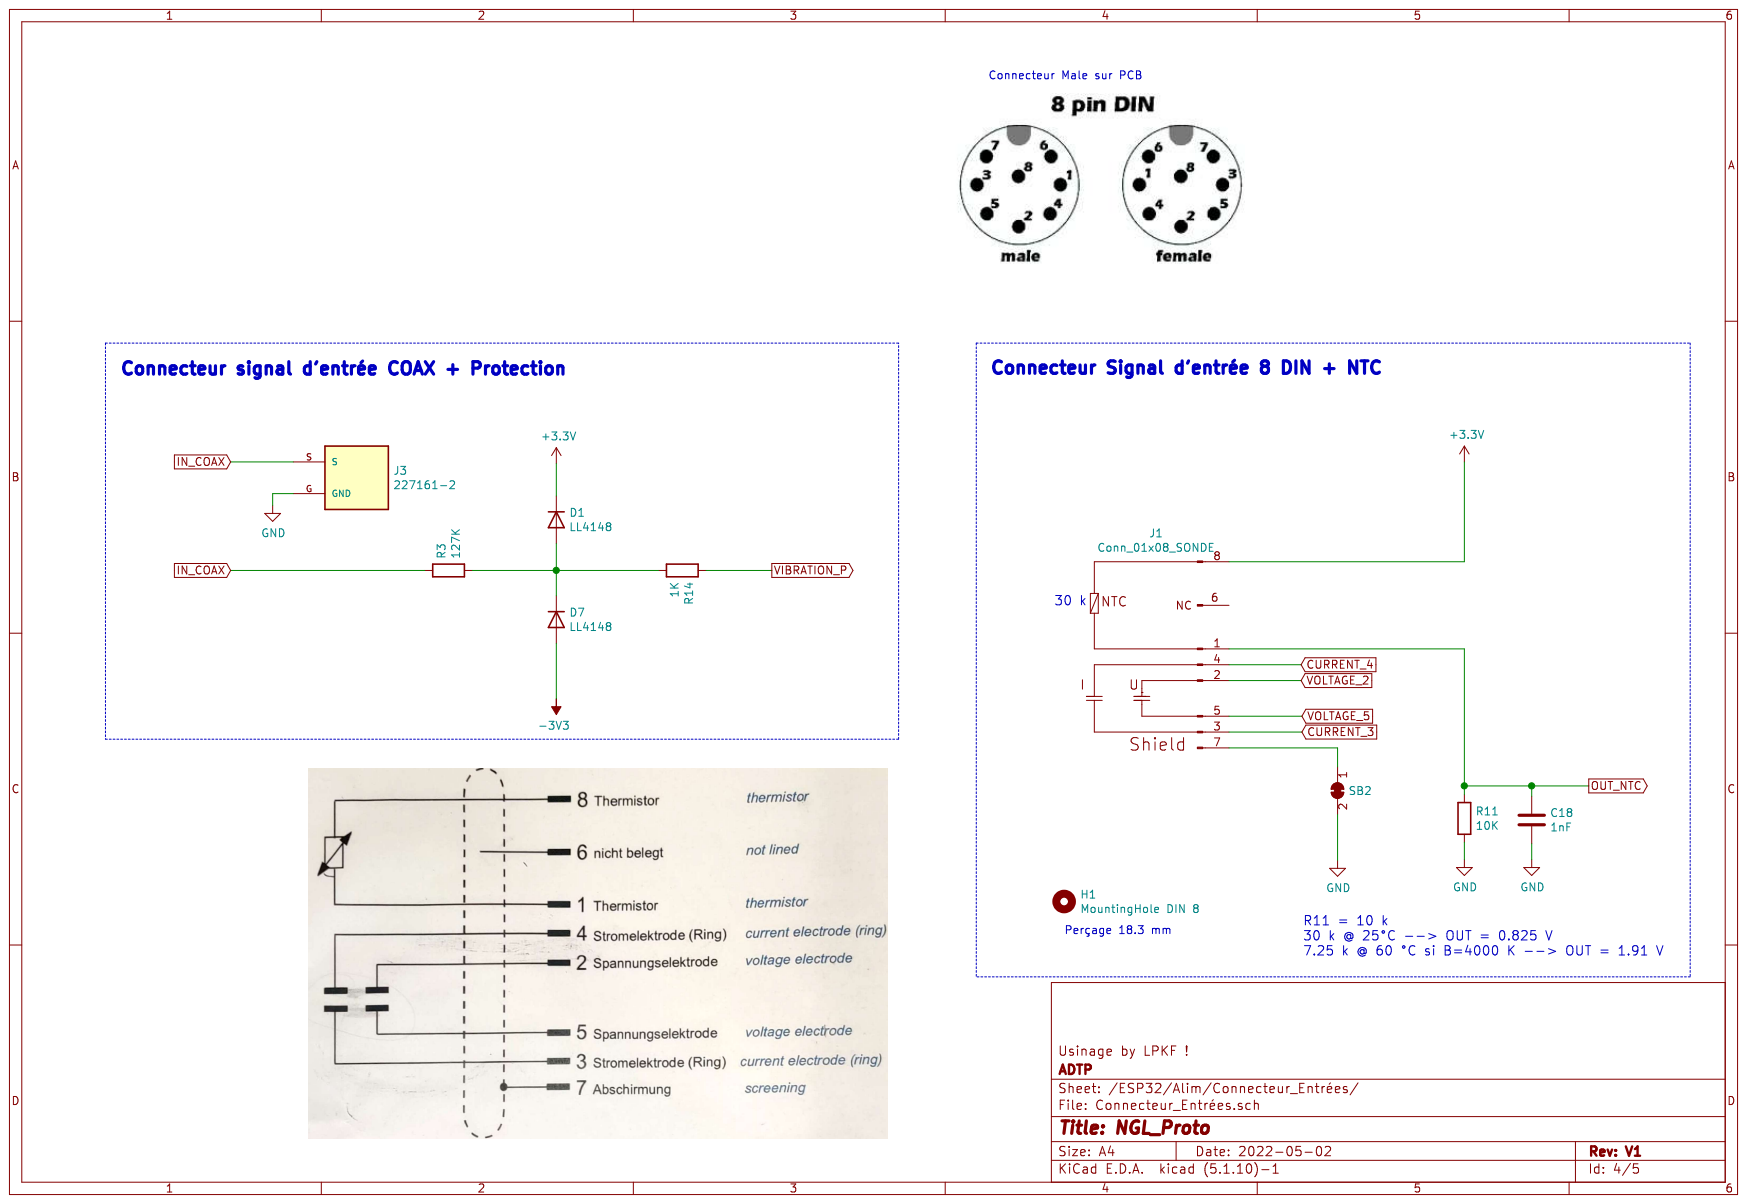
[picture p46: page 4]

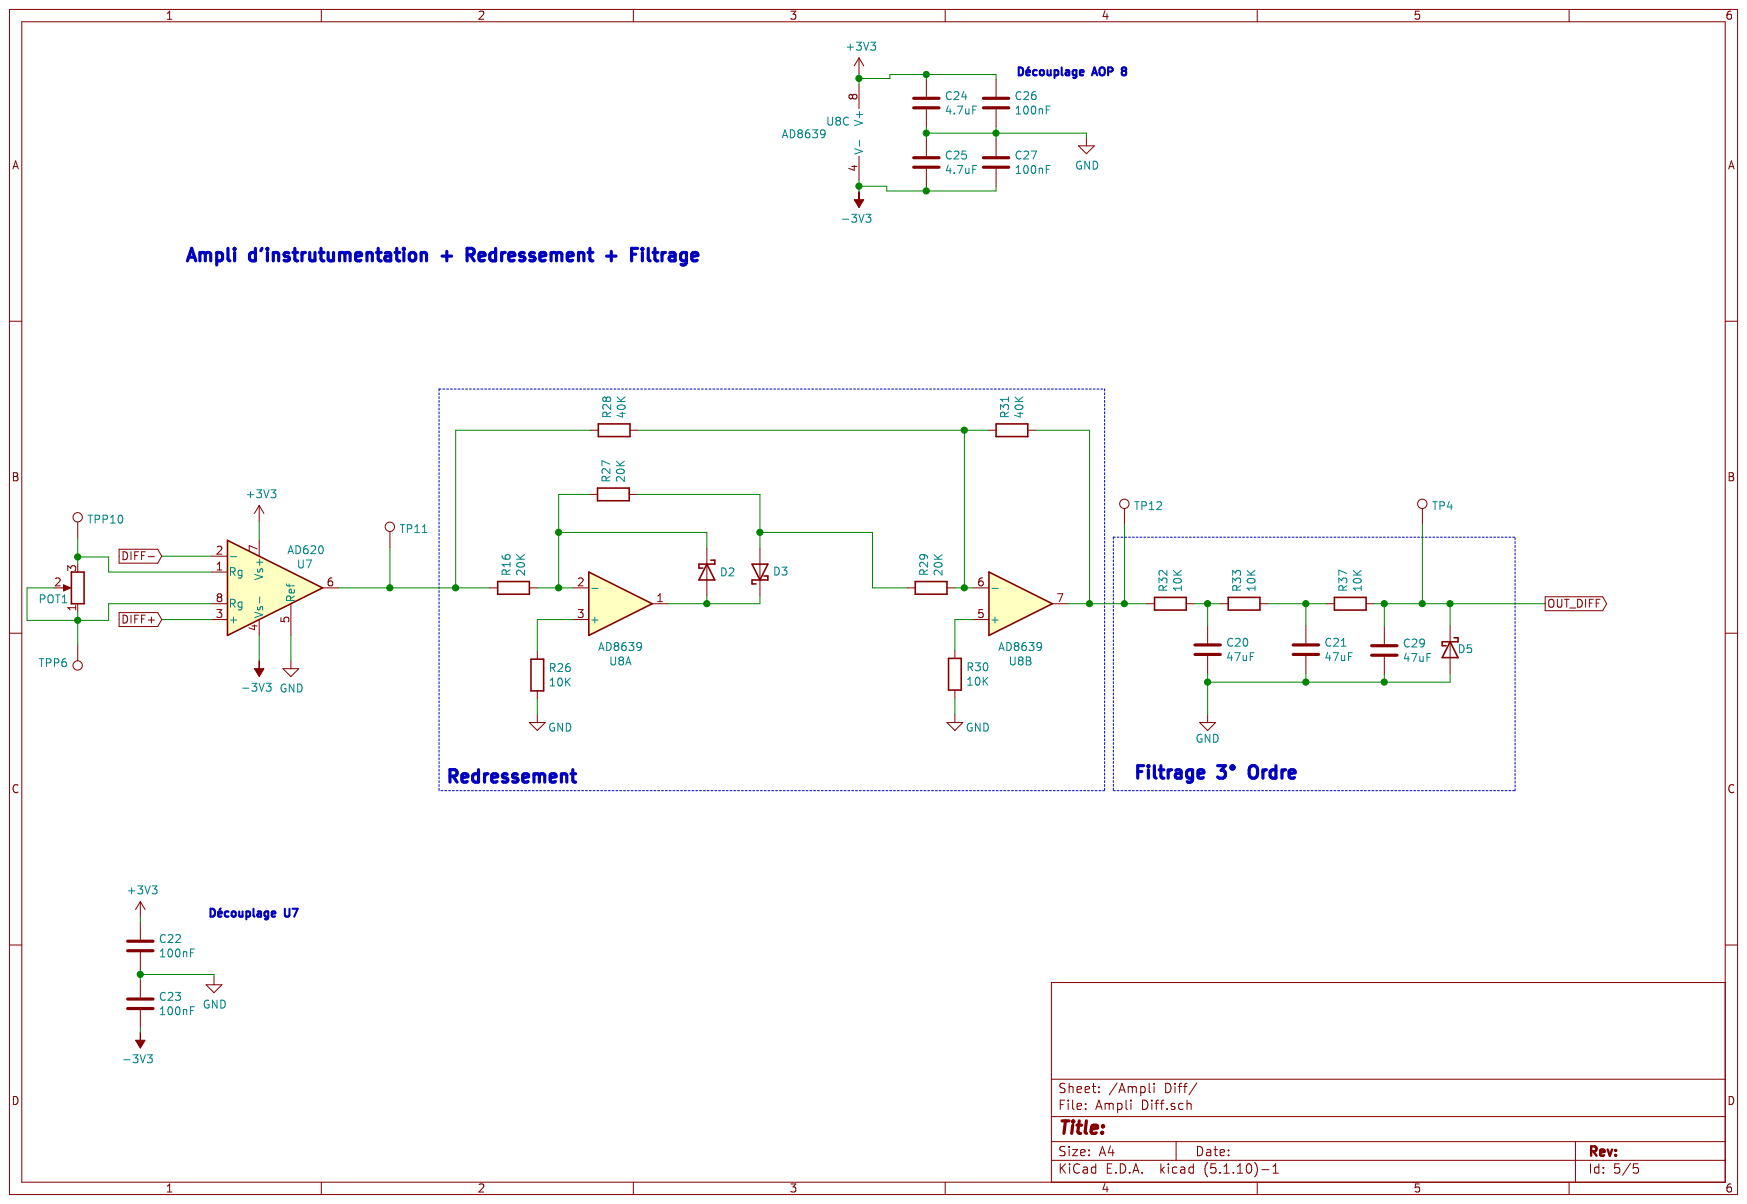
[picture p47: page 5]
