benoitGIRAUD/NGL_PROTO_ST/Output/SILKSCREEN/Silk_BOT.pdf

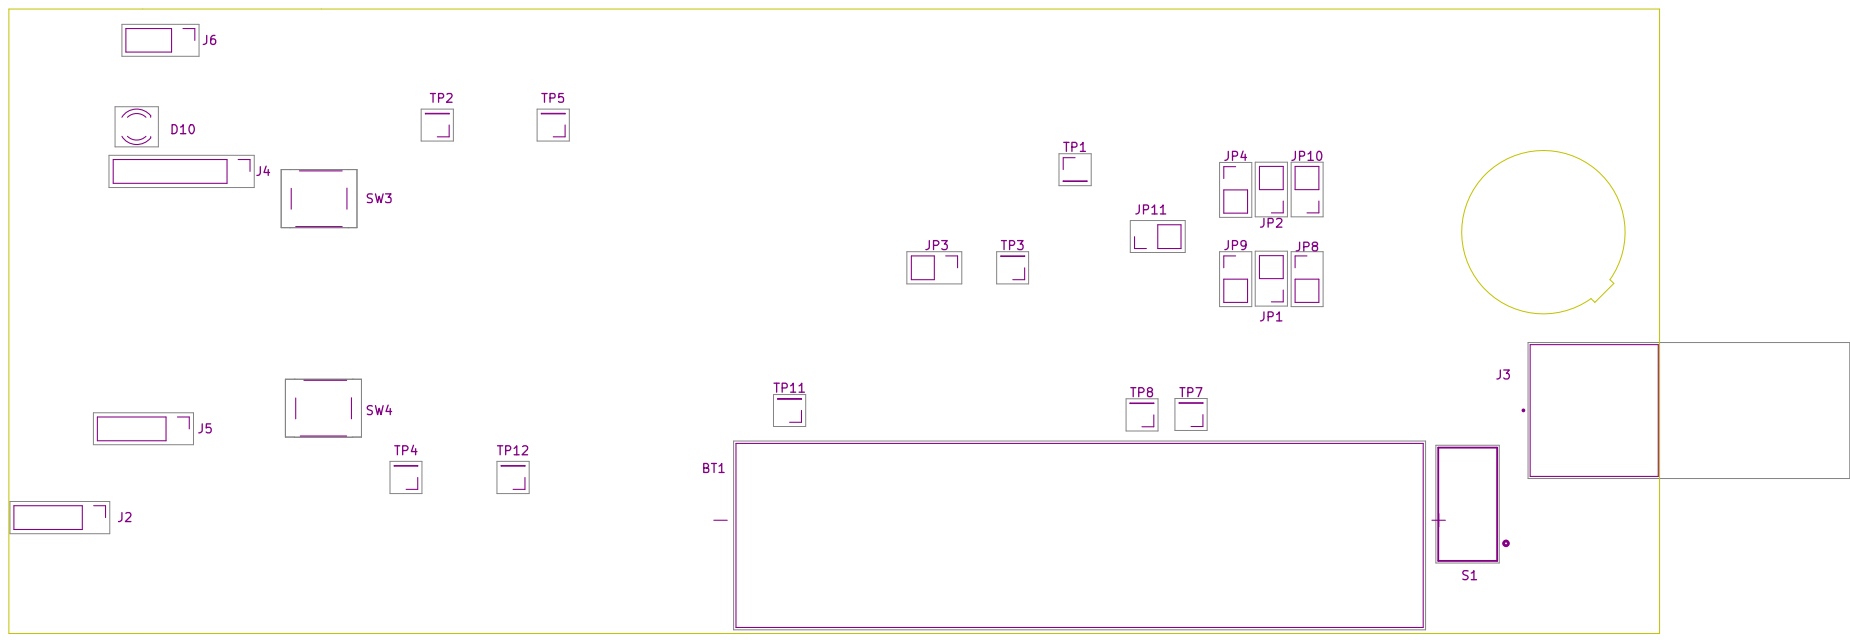
[picture p48: page 1]
