benoitGIRAUD/NGL_PROTO_ST/Output/SILKSCREEN/Silk_TOP.pdf

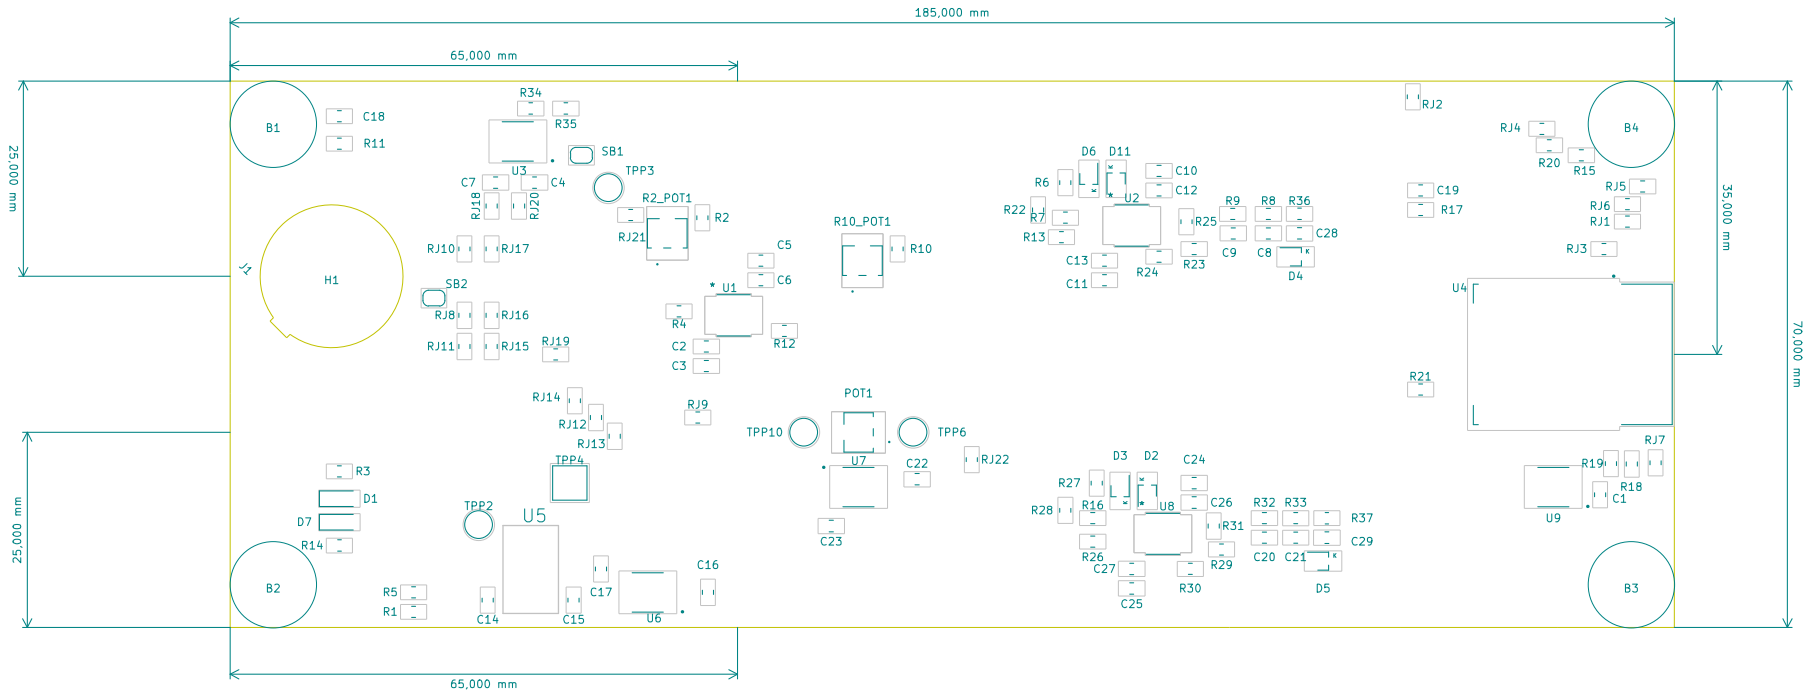
[picture p49: page 1]
