benoitGIRAUD/NGL_PROTO_ST/Output/SCH/NGL_Proto_V1_10-05.pdf

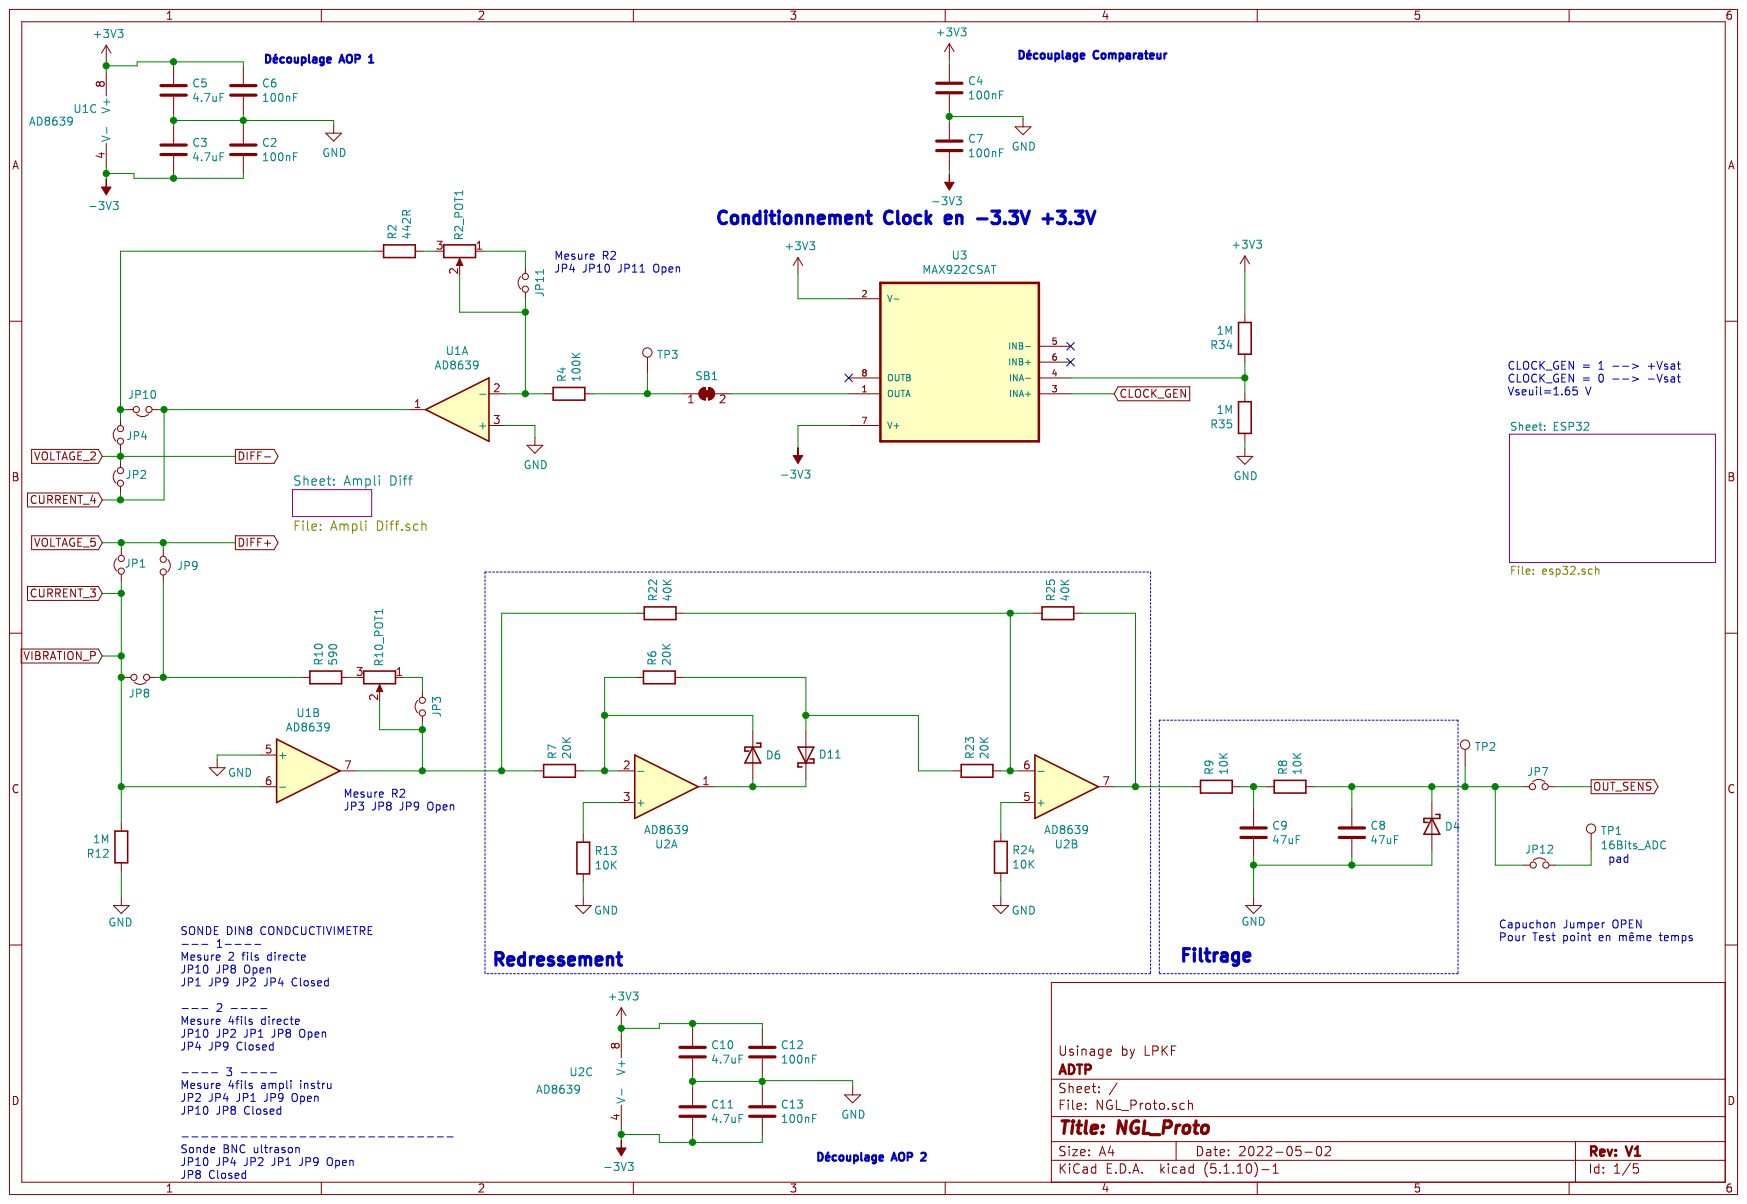
[picture p50: page 1]

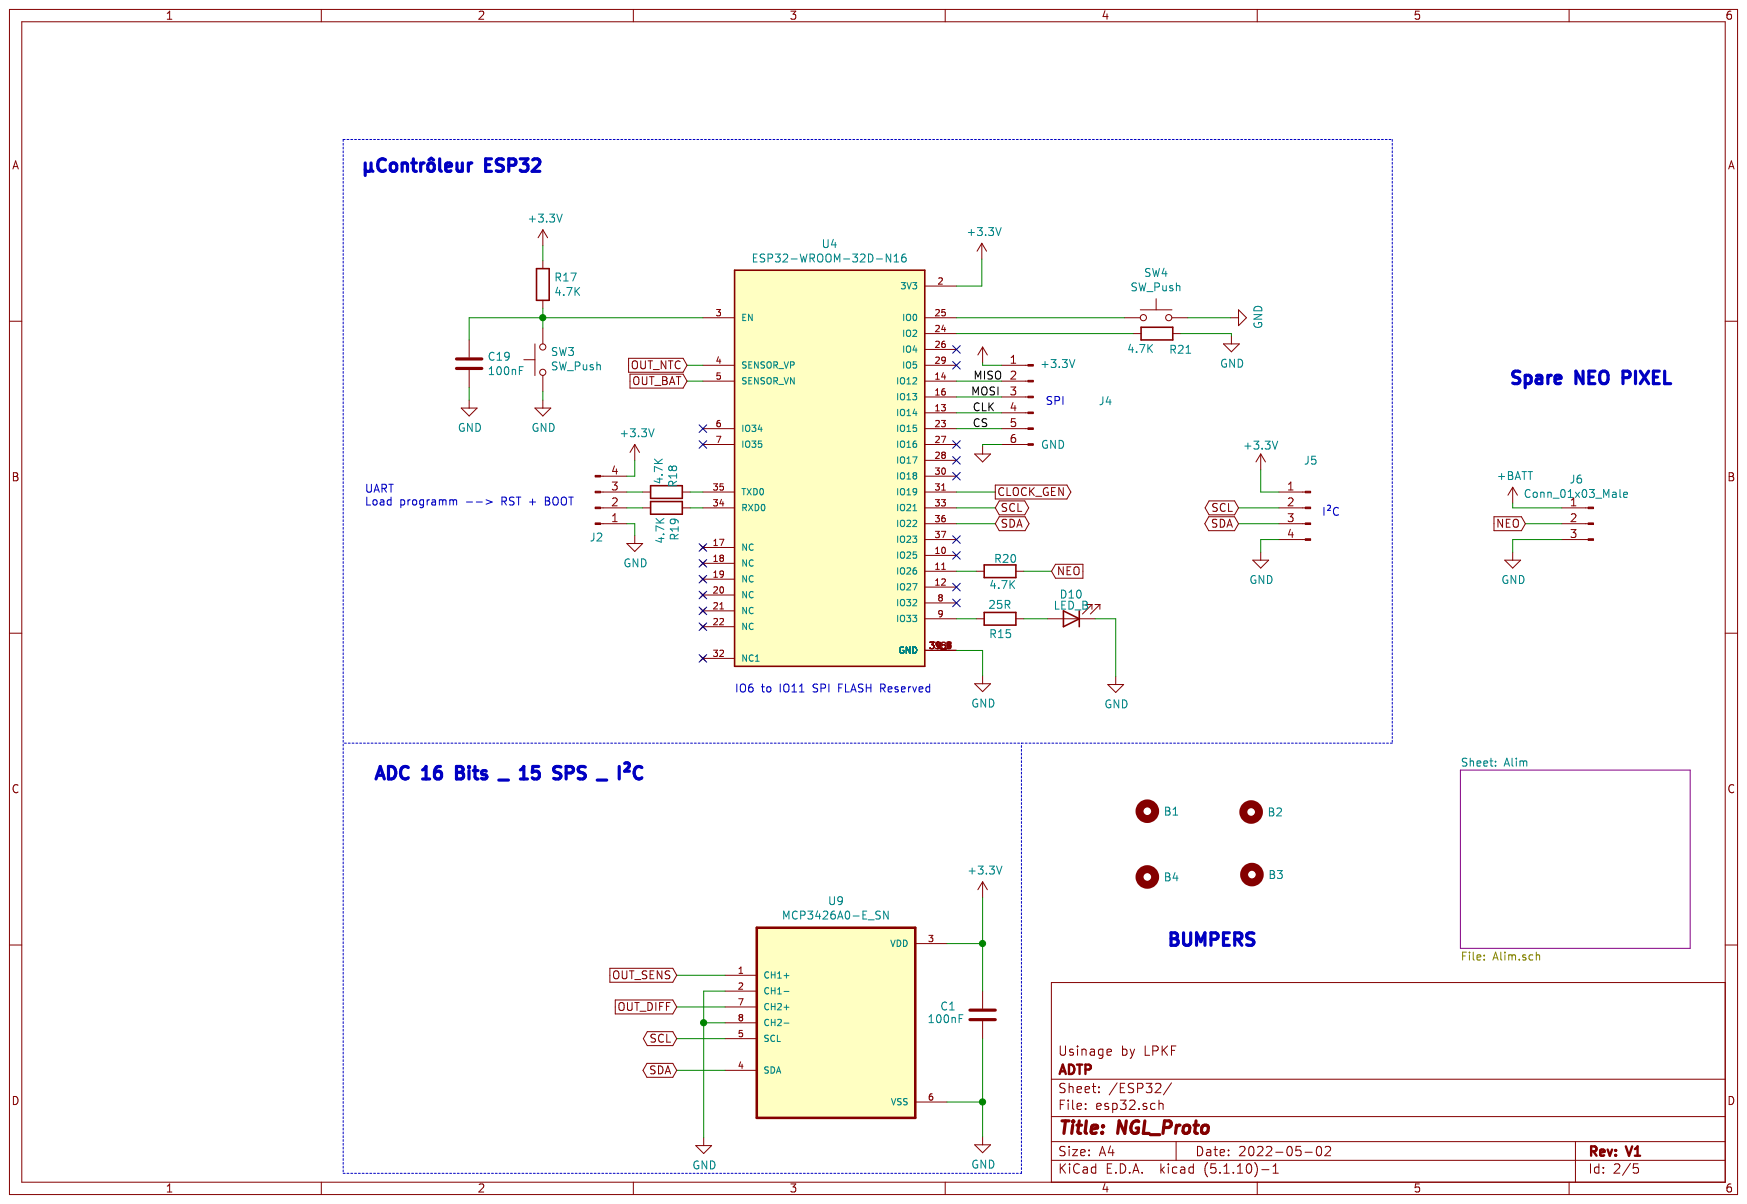
[picture p51: page 2]

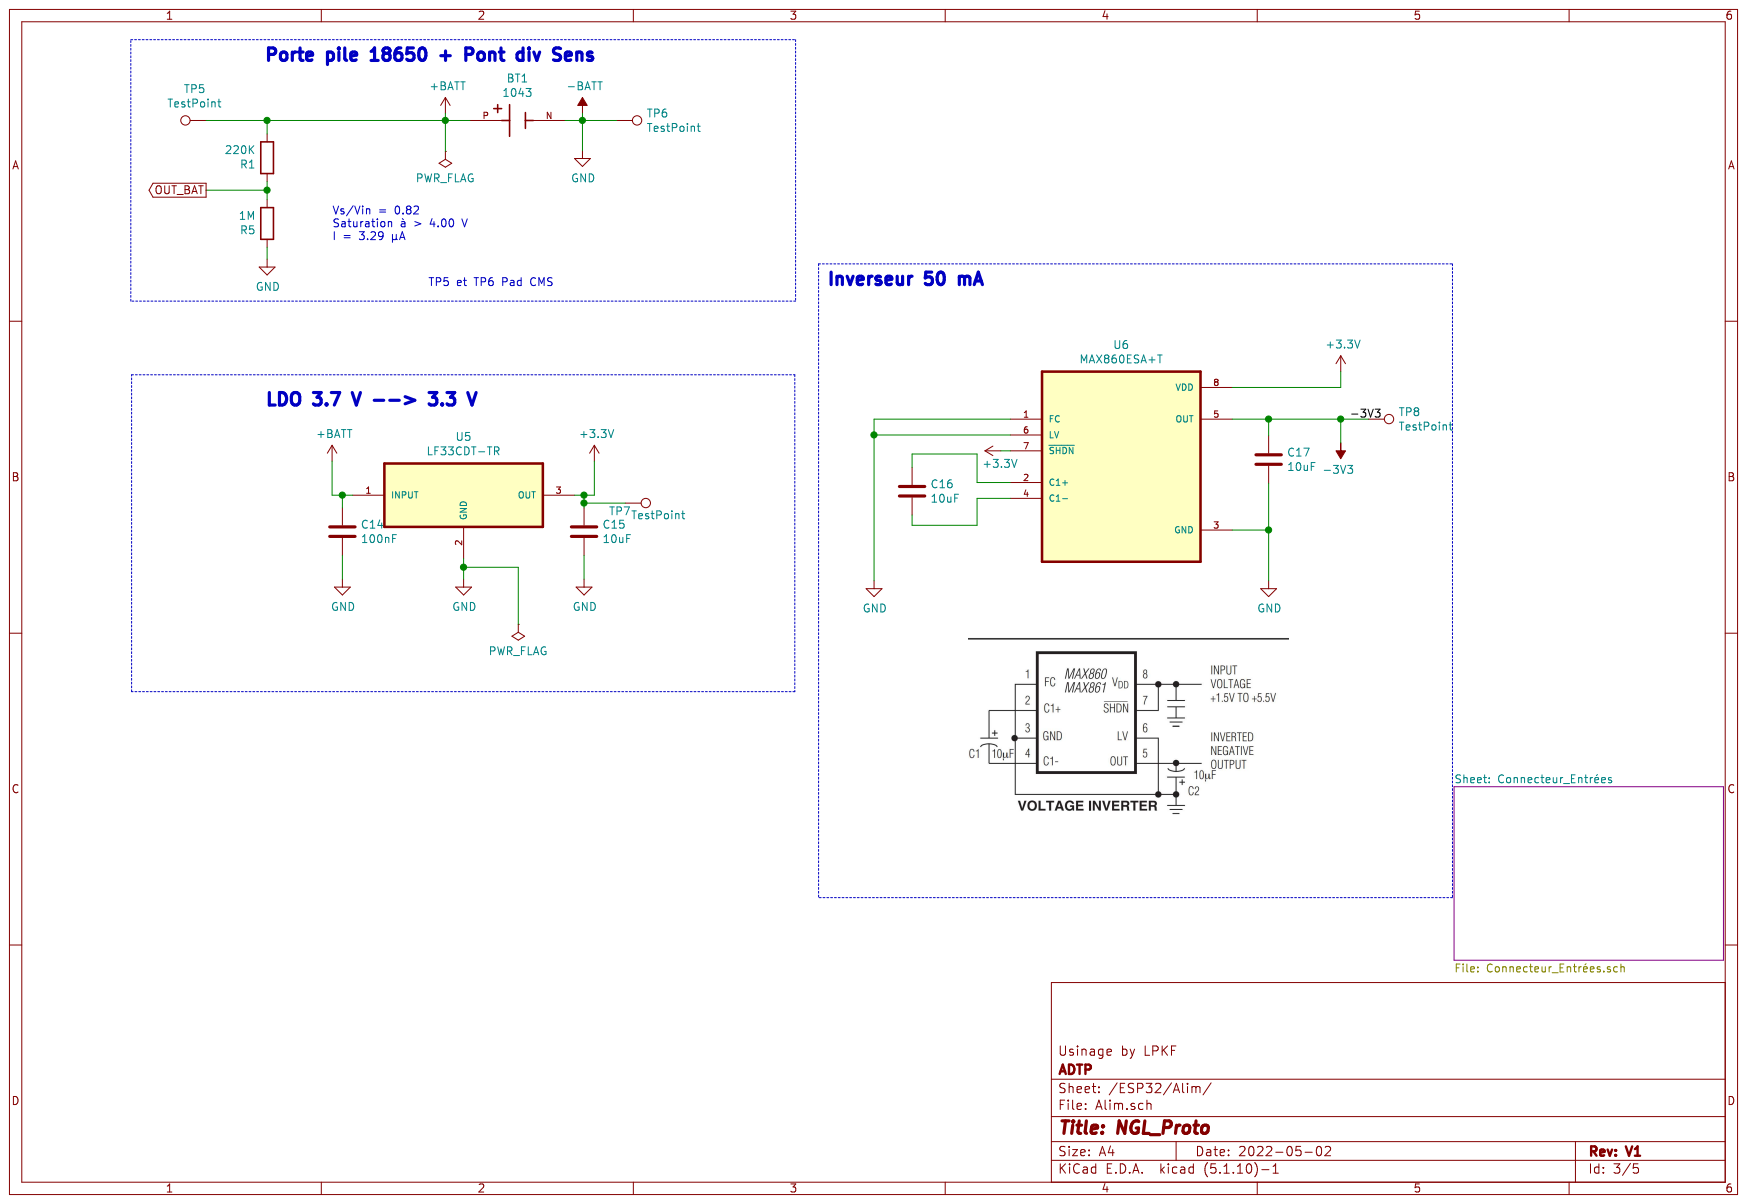
[picture p52: page 3]

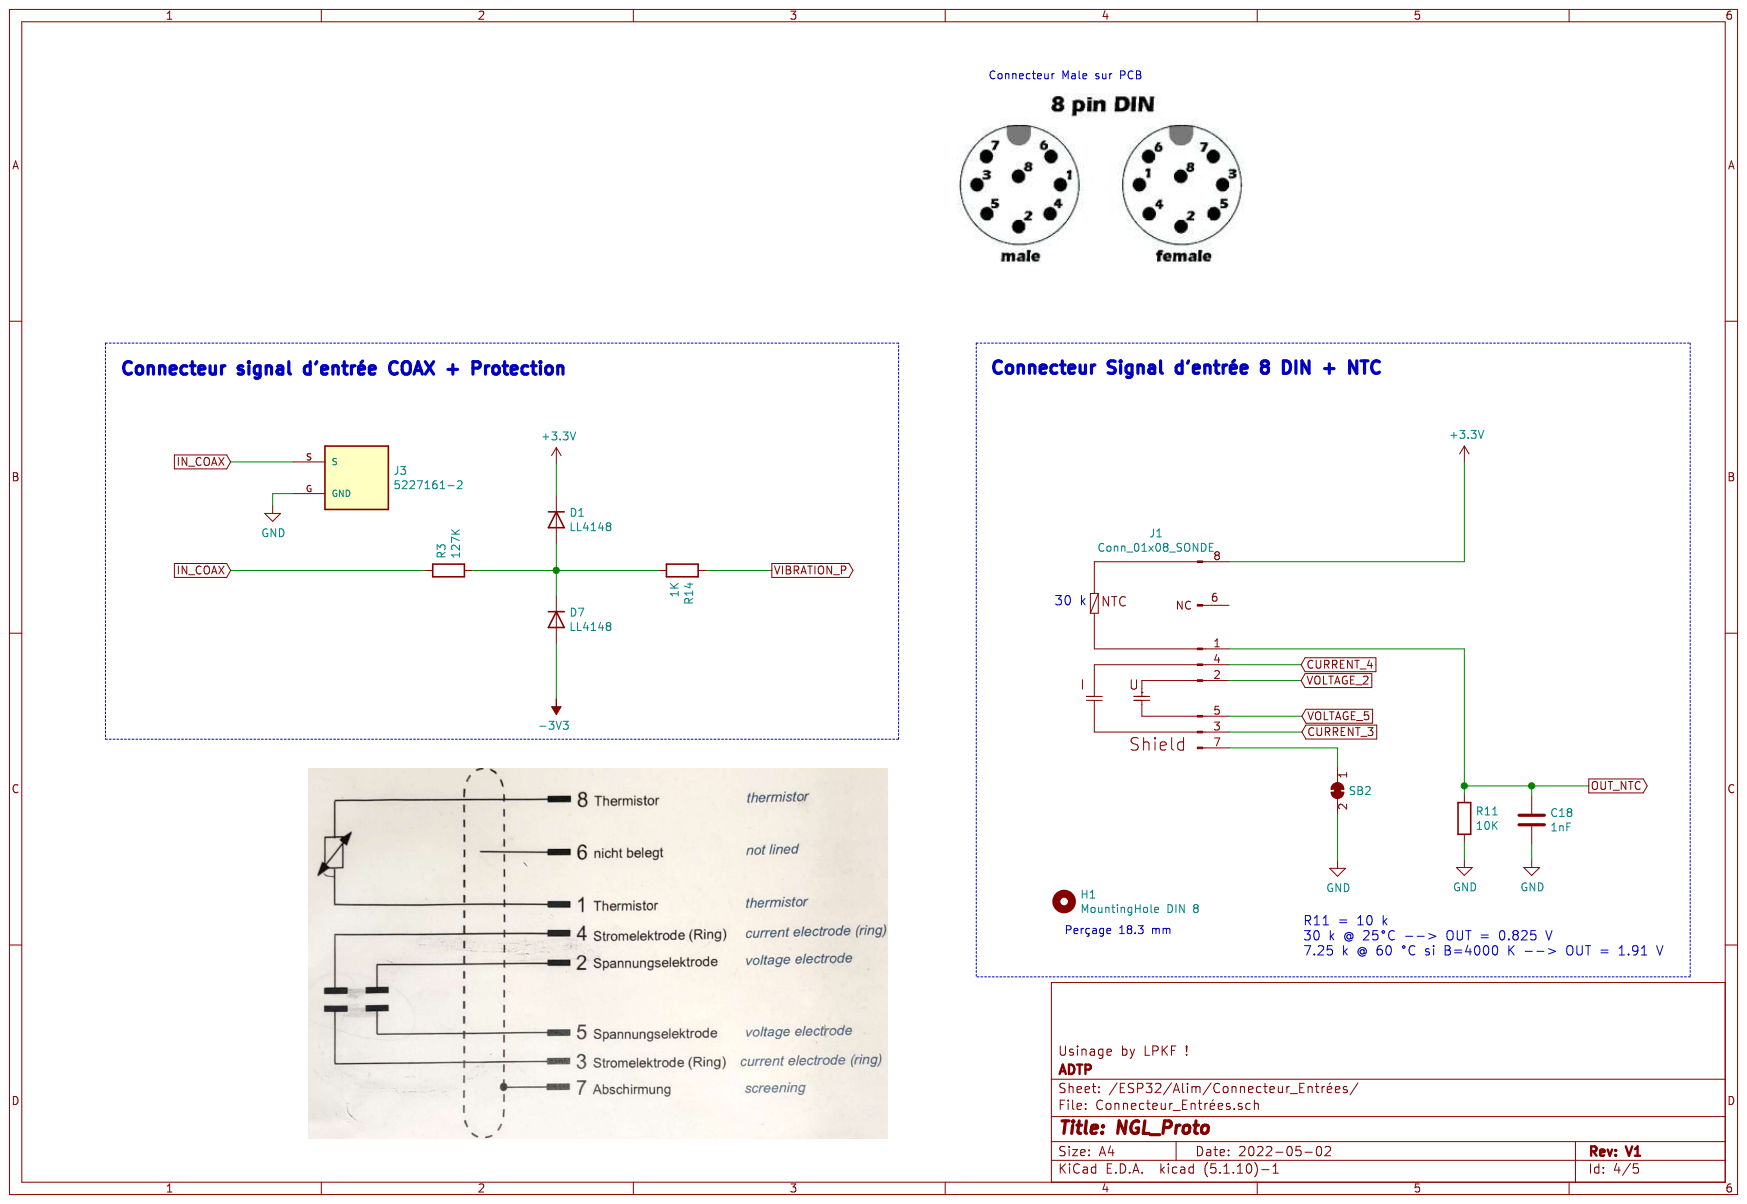
[picture p53: page 4]

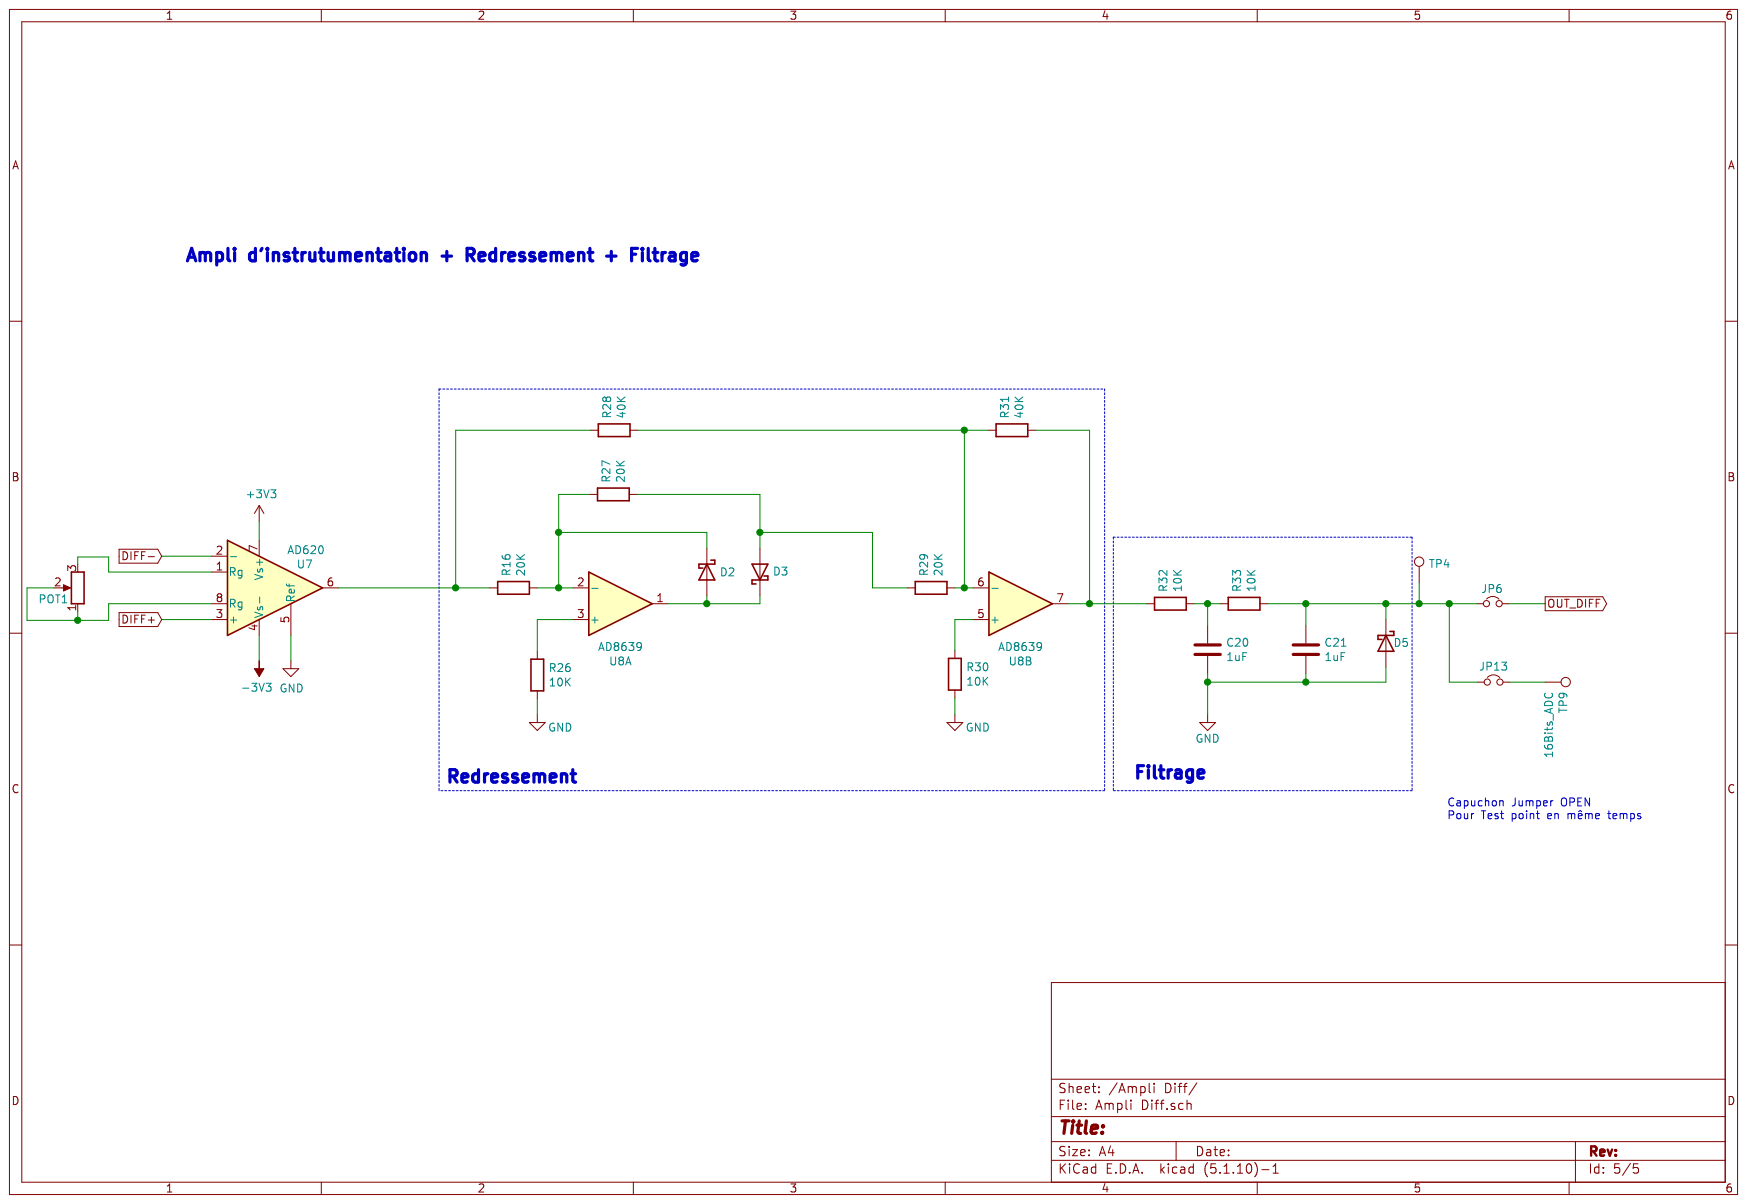
[picture p54: page 5]
